harbaum/ftduino/addons/i2c-expander/ftduino+txt.jpg

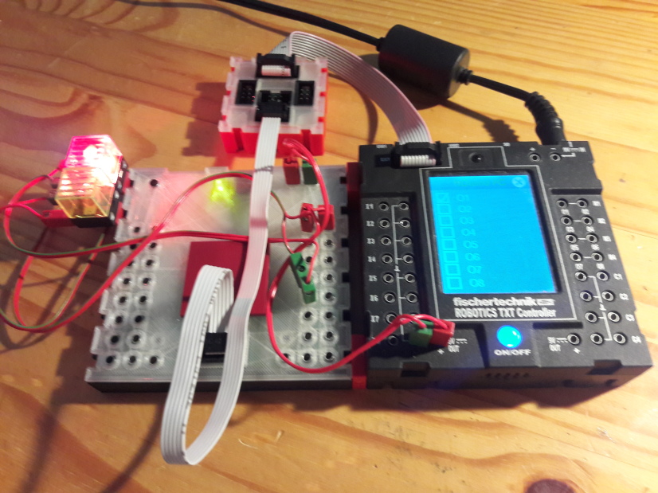
addons/i2c-expander/ftduino+txt.jpg
