harbaum/ftduino/doc/beispiele_ftduino.png

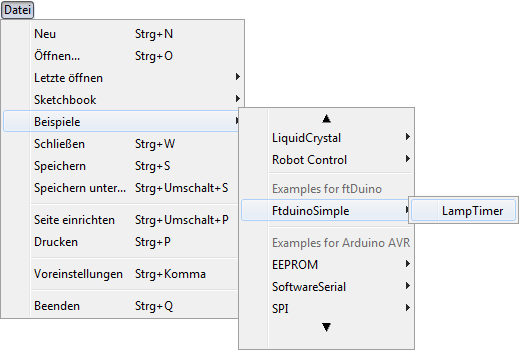
doc/beispiele_ftduino.png
