harbaum/ftduino/doc/ftduino_pcb_1.0.jpg

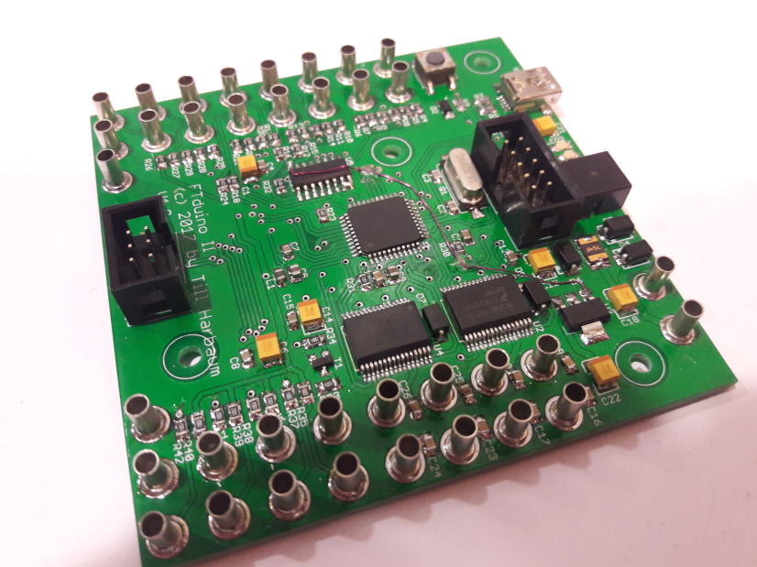
doc/ftduino_pcb_1.0.jpg
