harbaum/ftduino/webusb/images/webusb_board.png

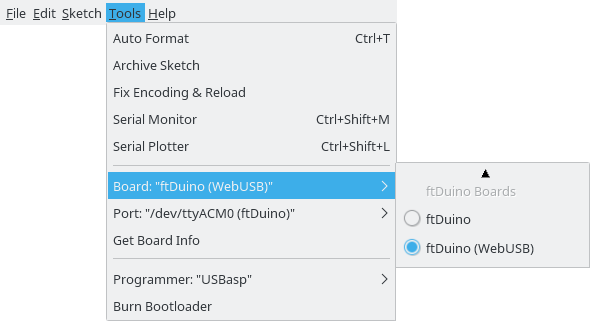
webusb/images/webusb_board.png
