harbaum/ftduino/webusb/images/webusb_examples.png

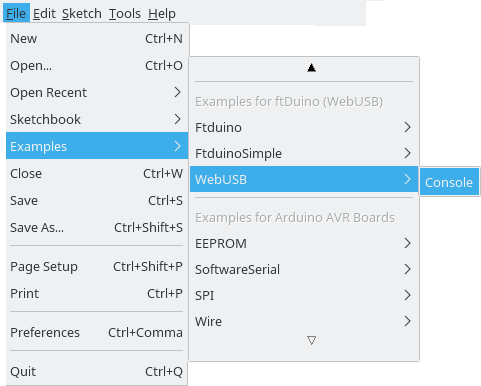
webusb/images/webusb_examples.png
