harbaum/ftduino/www/blue/images/ftduino_modul.jpg

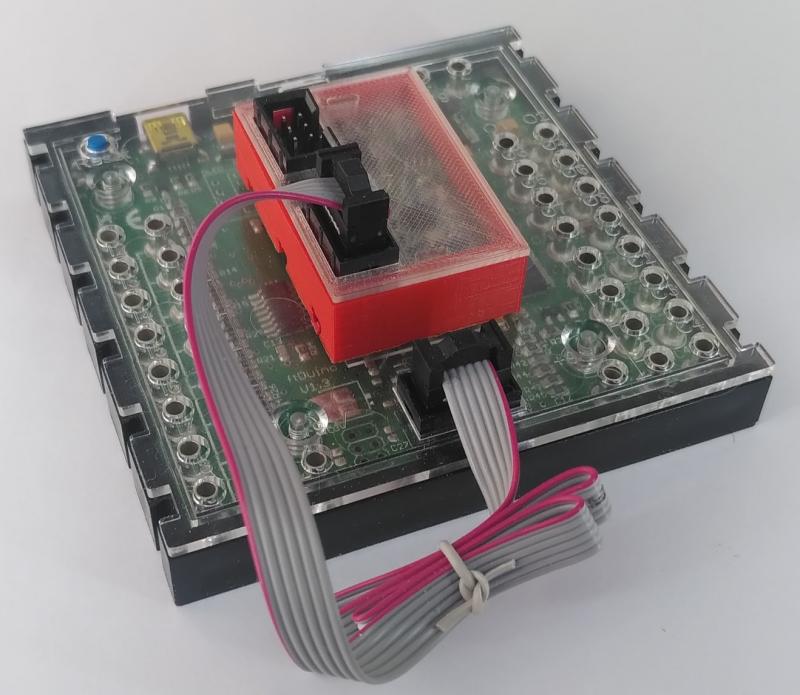
www/blue/images/ftduino_modul.jpg
