harbaum/ftduino/www/blue/images/ftduino_robot.jpg

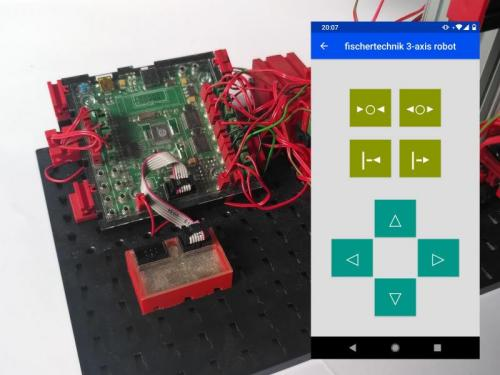
www/blue/images/ftduino_robot.jpg
