harbaum/ftduino/www/blue/images/ftduinoblue_buttons.png

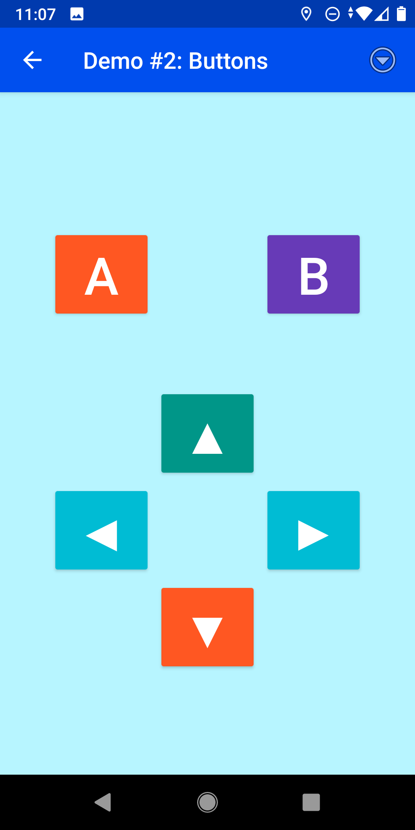
www/blue/images/ftduinoblue_buttons.png
