harbaum/ftduino/www/blue/images/ftduinoblue_demos.png

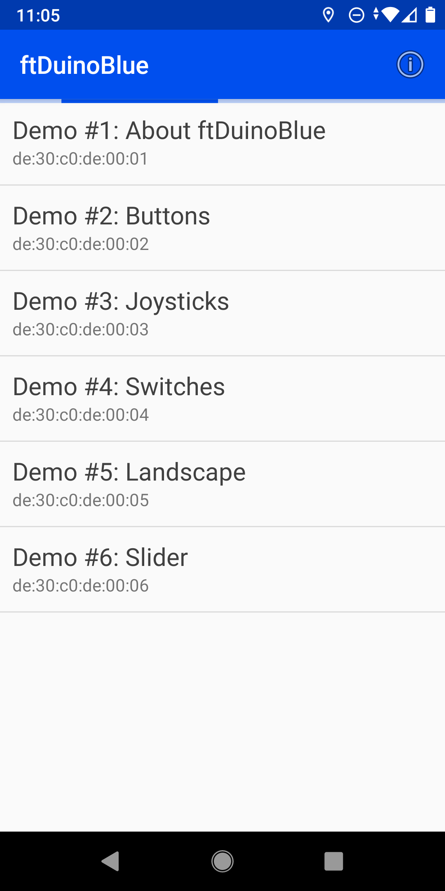
www/blue/images/ftduinoblue_demos.png
