harbaum/ftduino/www/blue/images/ftduinoblue_init.png

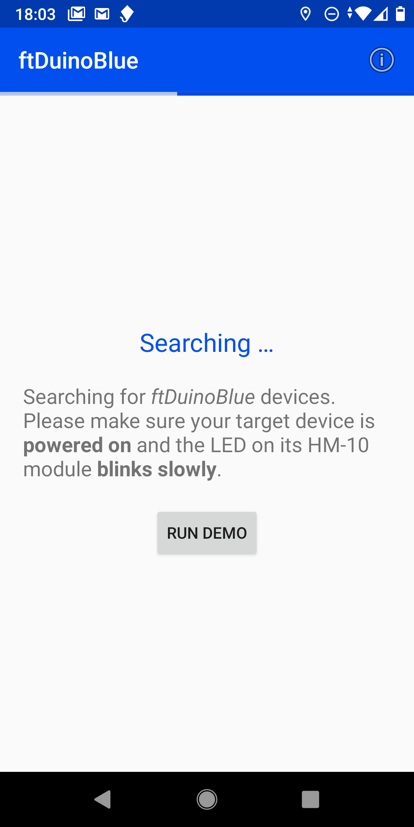
www/blue/images/ftduinoblue_init.png
