harbaum/ftduino/www/blue/images/ftduinoblue_introduction.png

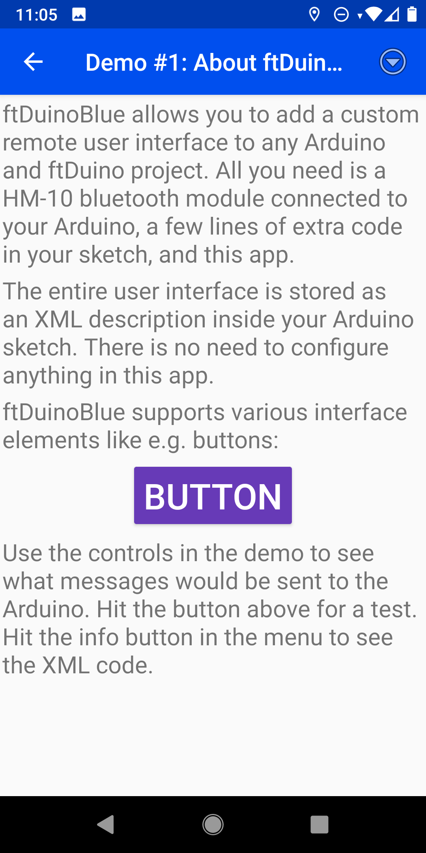
www/blue/images/ftduinoblue_introduction.png
