harbaum/ftduino/www/blue/images/ftduinoblue_joystick.png

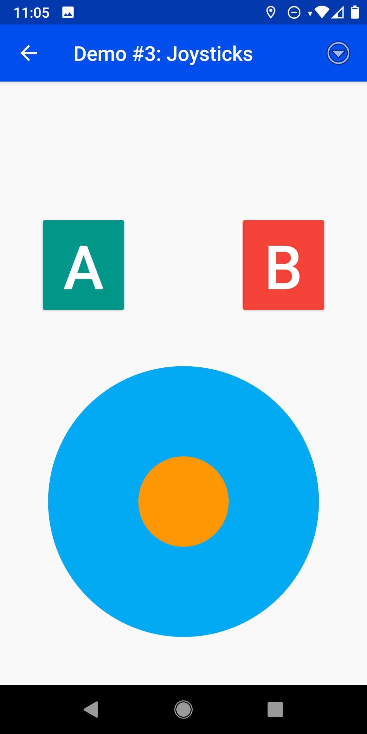
www/blue/images/ftduinoblue_joystick.png
