harbaum/ftduino/www/blue/images/ftduinoblue_landscape.png

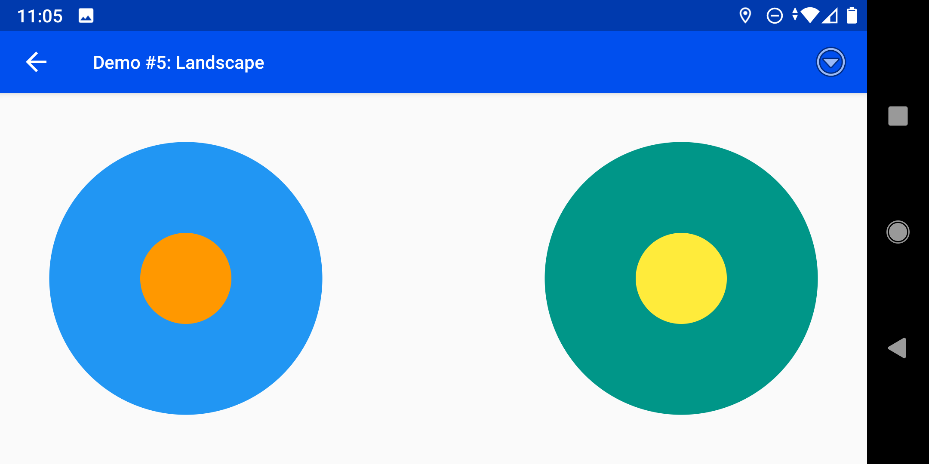
www/blue/images/ftduinoblue_landscape.png
