harbaum/ftduino/www/blue/images/ftduinoblue_sliders.png

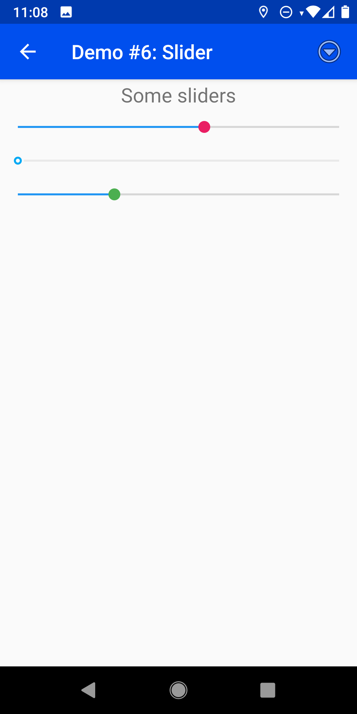
www/blue/images/ftduinoblue_sliders.png
