harbaum/ftduino/www/blue/images/ftduinoblue_switches.png

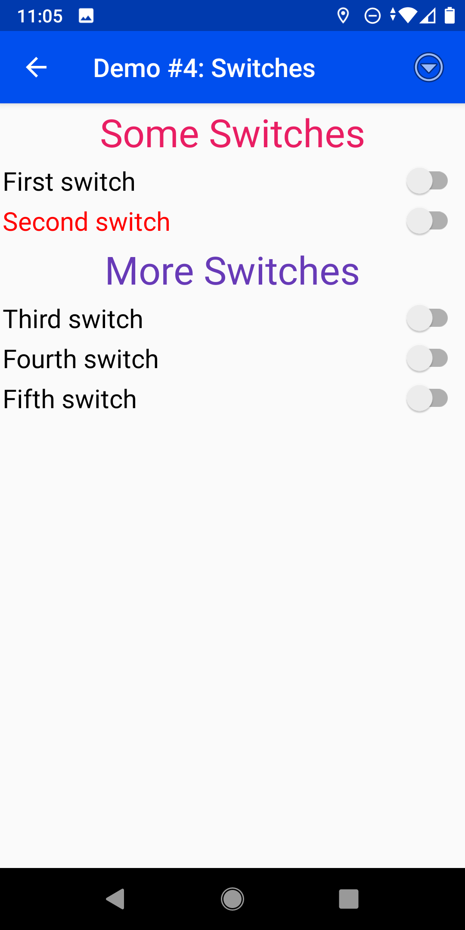
www/blue/images/ftduinoblue_switches.png
