harbaum/ftduino/www/blue/images/ftduinoblue_uno.jpg

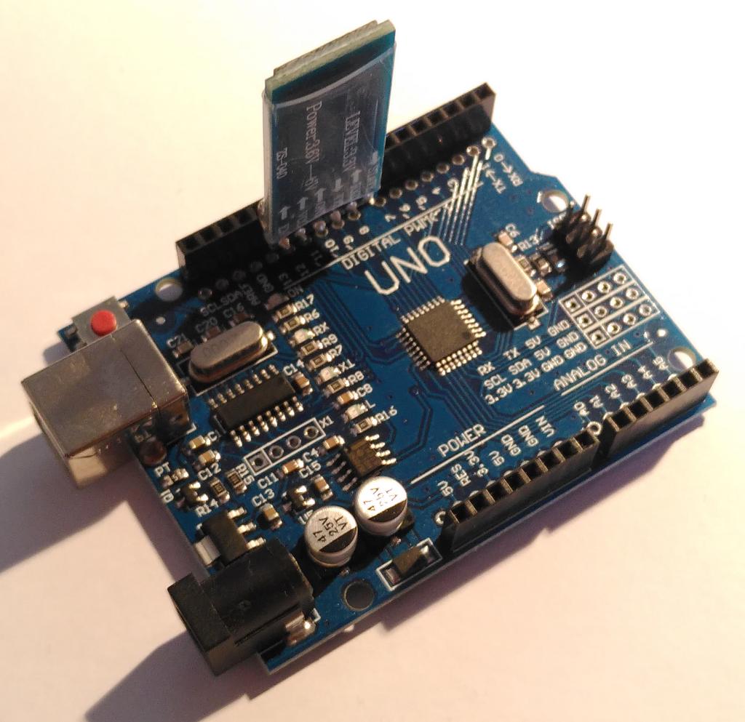
www/blue/images/ftduinoblue_uno.jpg
