harbaum/ftduino/www/blue/images/ftduinoblue_uno.png

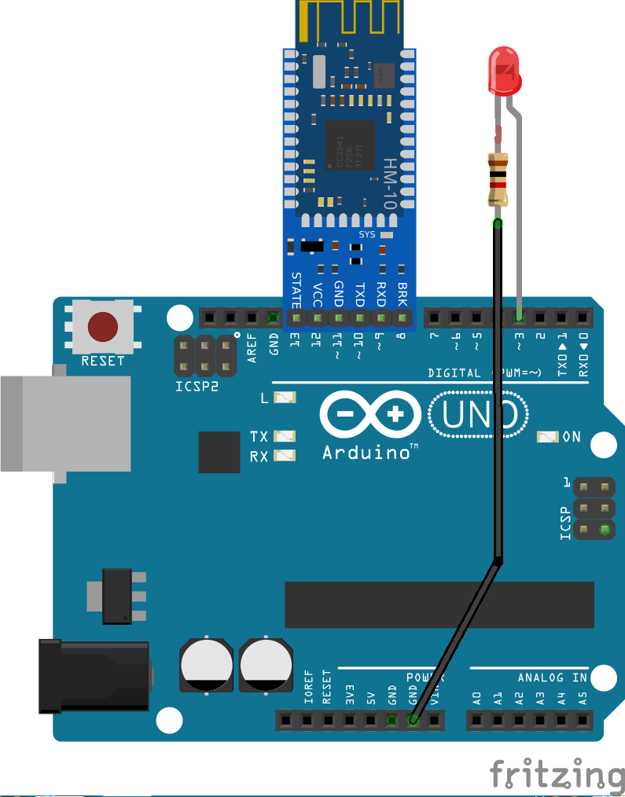
www/blue/images/ftduinoblue_uno.png
