harbaum/ftduino/www/blue/images/screenshot_demo.png

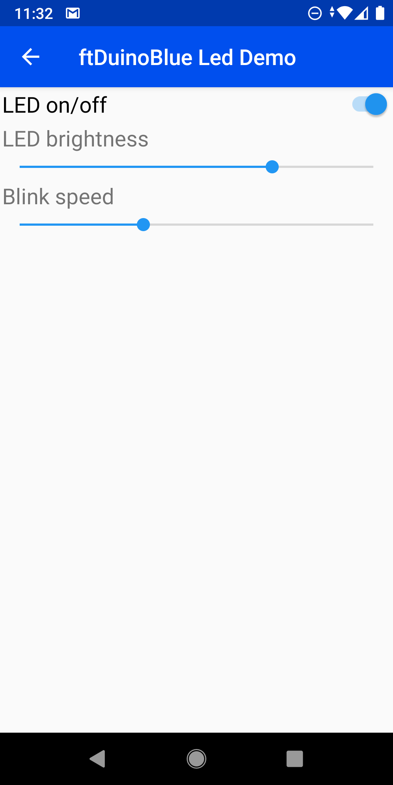
www/blue/images/screenshot_demo.png
