harbaum/ftduino/www/images/anschluesse.png

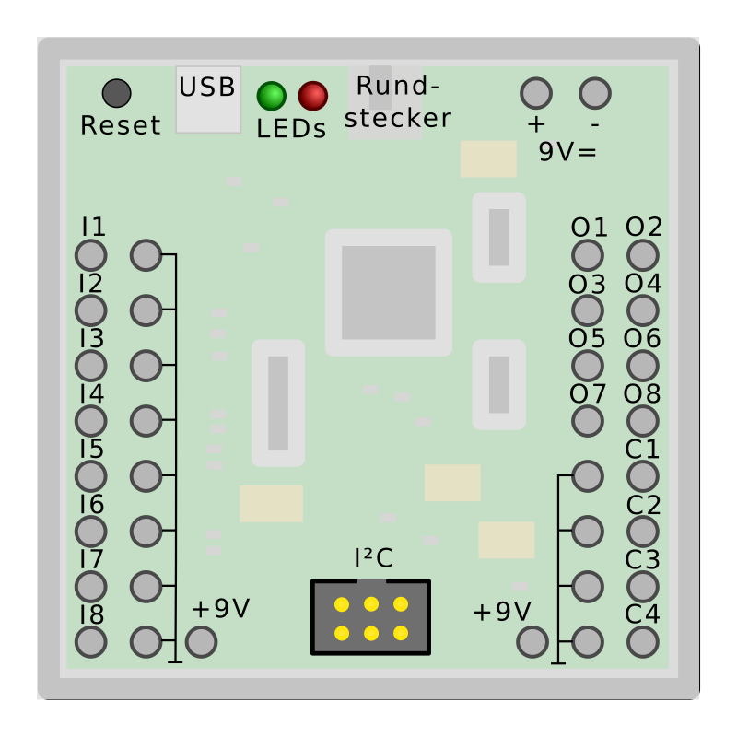
www/images/anschluesse.png
