harbaum/ftduino/www/images/ftduino.jpg

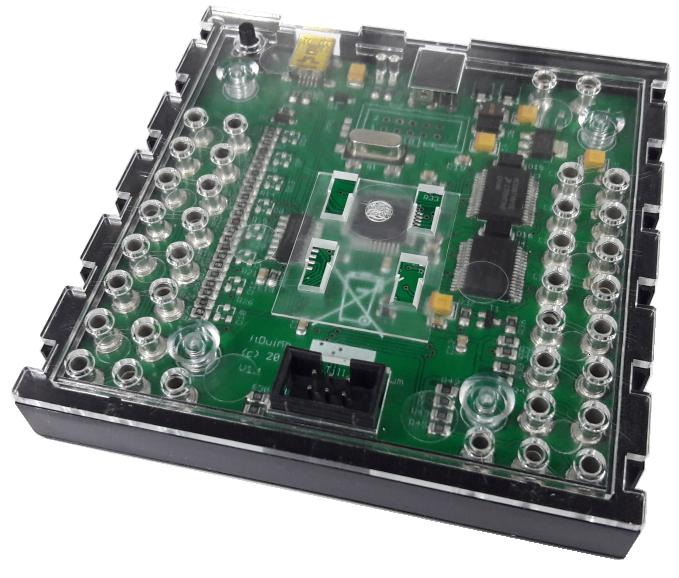
www/images/ftduino.jpg
