harbaum/ftduino/www/images/ide.png

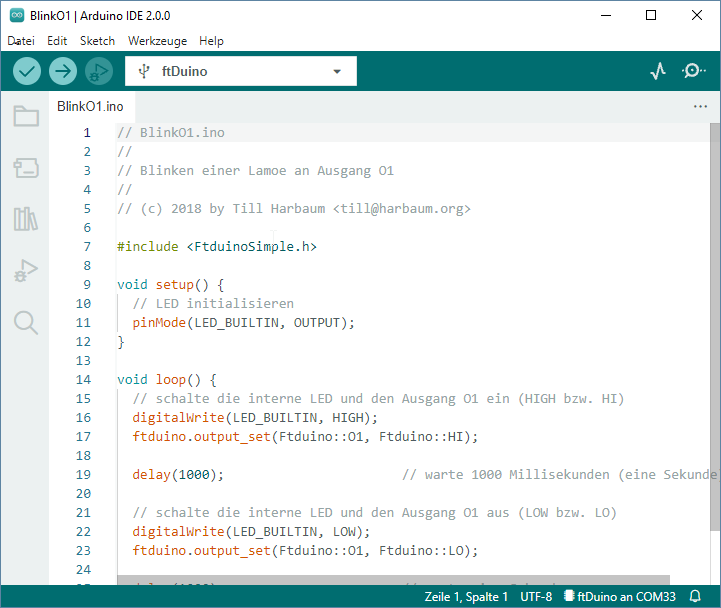
www/images/ide.png
