harbaum/ftduino/www/images/minecraft.jpg

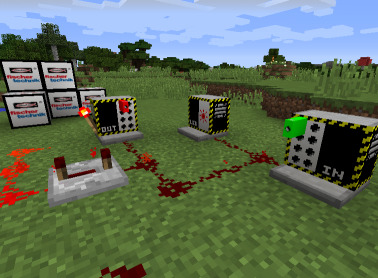
www/images/minecraft.jpg
