harbaum/ftduino/www/images/s4a_sprite.png

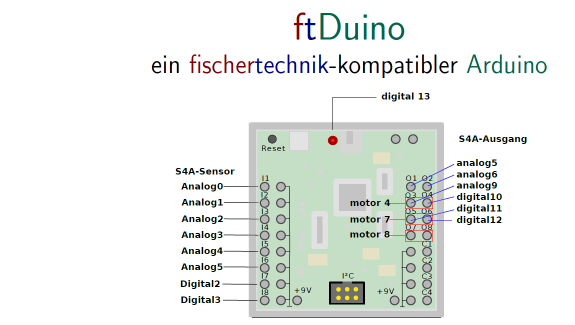
www/images/s4a_sprite.png
