harbaum/ftduino/www/images/scratch3_ftduino1.png

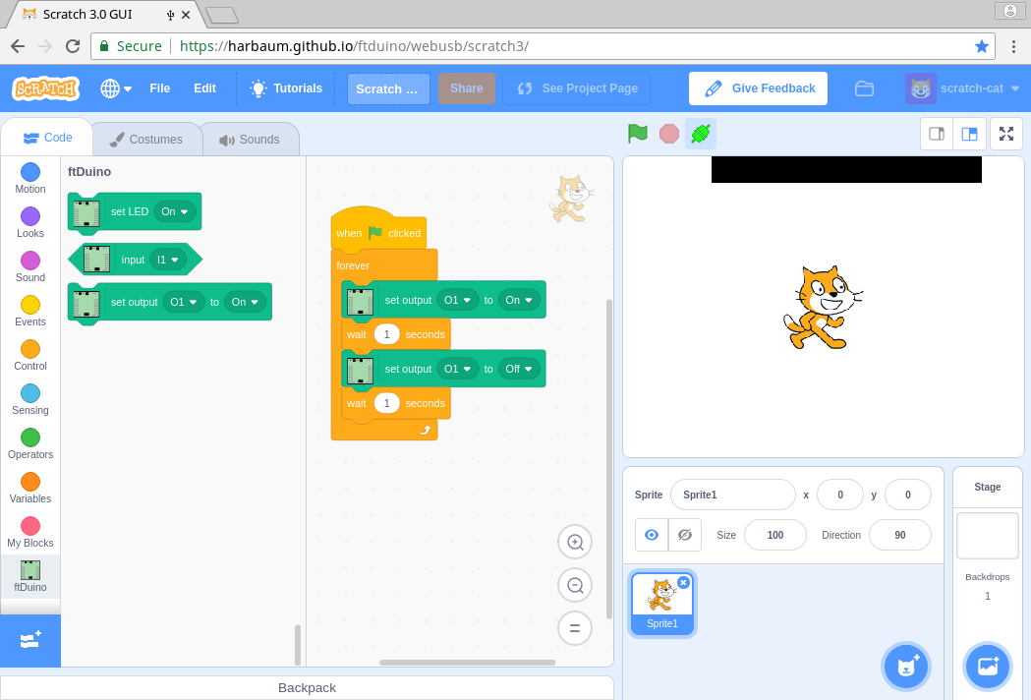
www/images/scratch3_ftduino1.png
