harbaum/ftduino/www/manual/anhang/ftduino_1_1_schematic_pdf.png

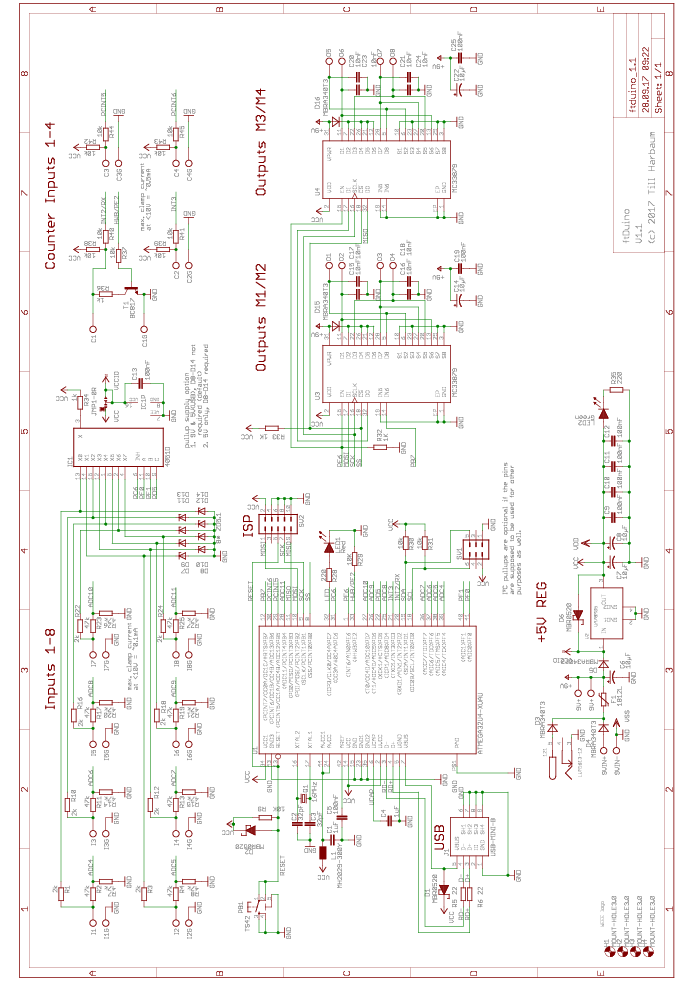
www/manual/anhang/ftduino_1_1_schematic_pdf.png
