harbaum/ftduino/www/manual/anhang/ftduino_1_1_parts_pdf.png

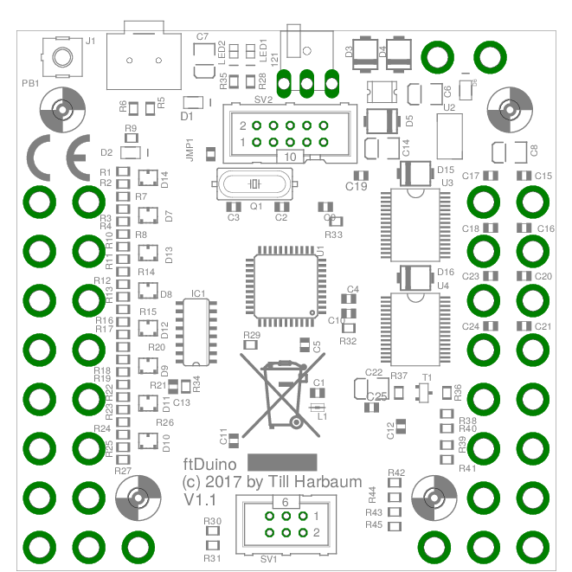
www/manual/anhang/ftduino_1_1_parts_pdf.png
