harbaum/ftduino/case/reset_button.stl

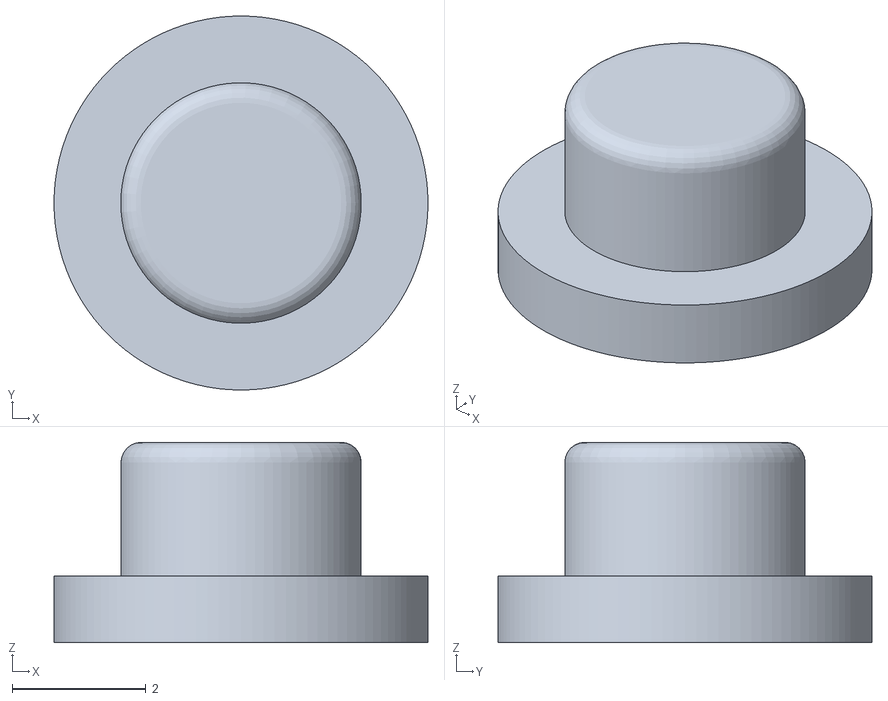
[picture p69: CAD file, 2017-12-19]
case/reset_button.stl
5.60 x 5.60 x 3.00
