harbaum/ftduino/case/bottom.stl

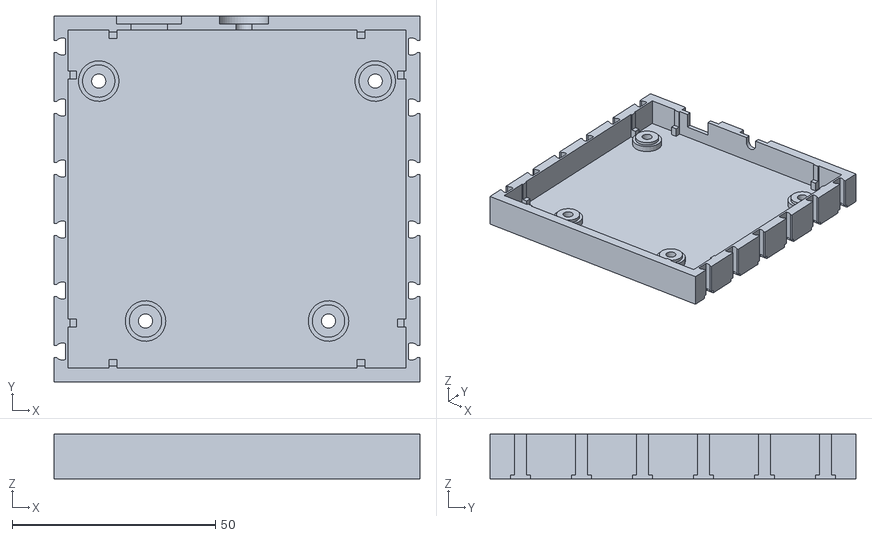
[picture p70: CAD file, 2017-12-19]
case/bottom.stl
90.0 x 90.0 x 11.0
