harbaum/ftduino/addons/vl53l0x/bottom.fcstd

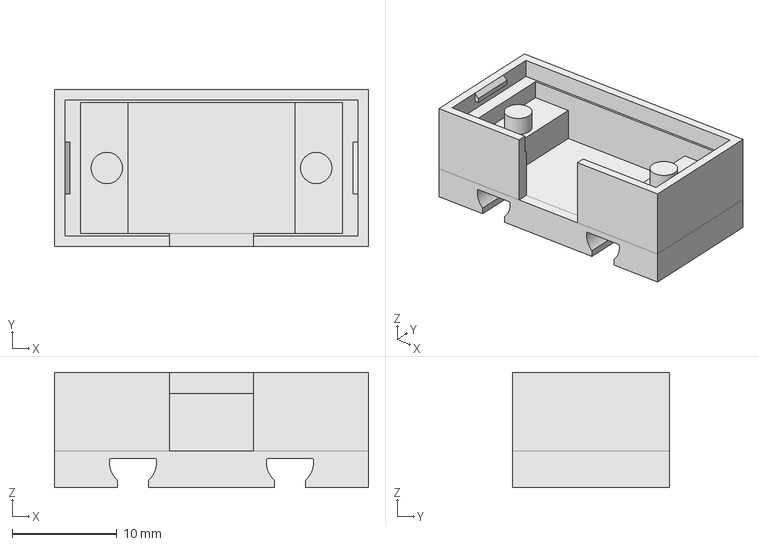
[picture p71: CAD file, 2018-03-22, an earlier design]
addons/vl53l0x/bottom.fcstd
30.0 x 15.0 x 11.0 mm
