harbaum/ftduino/www/manual/anhang/bottom_drawing_pdf.png

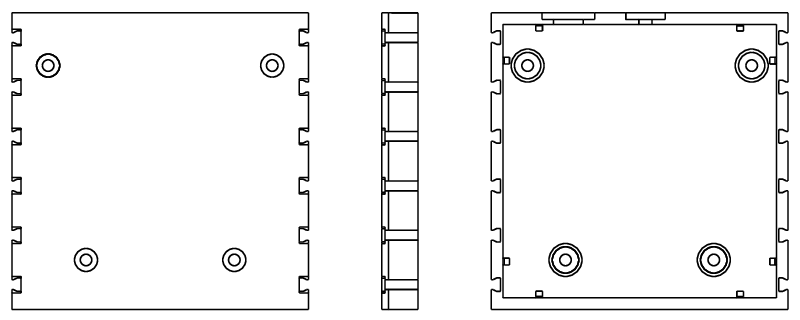
www/manual/anhang/bottom_drawing_pdf.png
