harbaum/ftduino/www/manual/anhang/ftduino_1_1_board_pdf.png

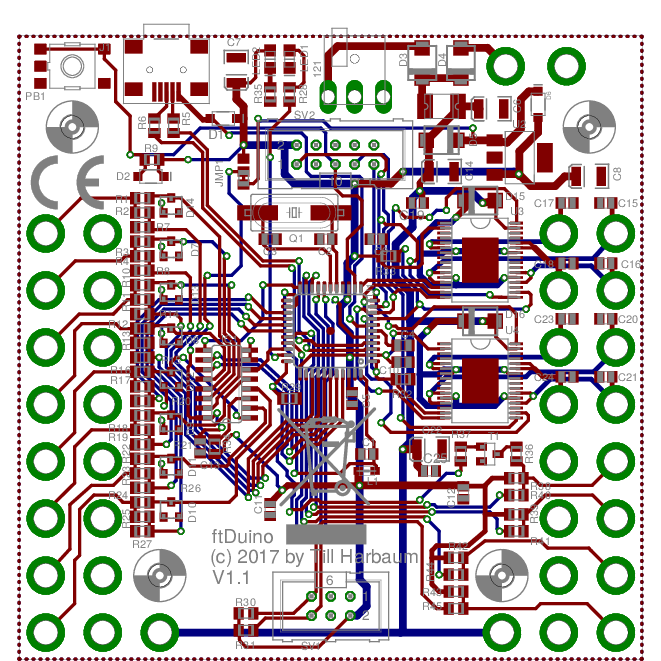
www/manual/anhang/ftduino_1_1_board_pdf.png
