harbaum/ftduino/www/manual/anhang/ftduino_1_1_dimensions_svg.png

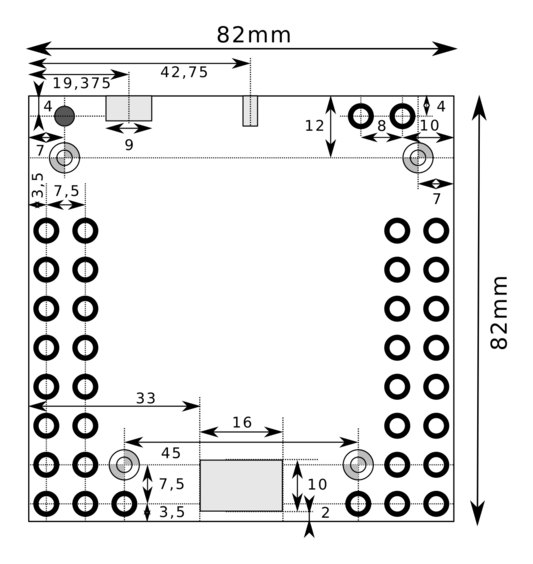
www/manual/anhang/ftduino_1_1_dimensions_svg.png
