harbaum/ftduino/www/manual/anhang/ftduino_1_1_masse_svg.png

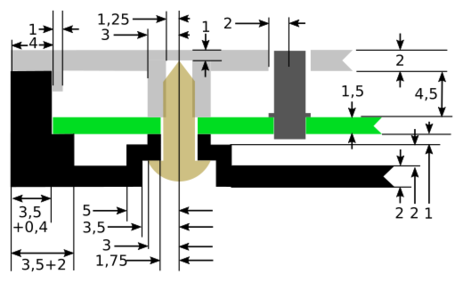
www/manual/anhang/ftduino_1_1_masse_svg.png
