harbaum/ftduino/www/manual/anhang/top_drawing_pdf.png

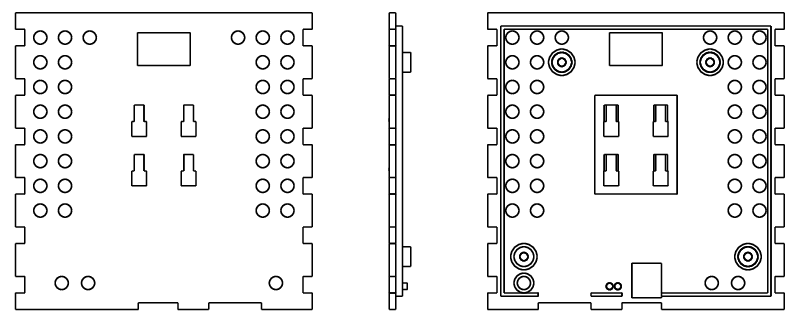
www/manual/anhang/top_drawing_pdf.png
