harbaum/ftduino/www/manual/aufbau/9v5v_svg.png

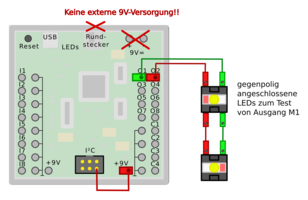
www/manual/aufbau/9v5v_svg.png
