harbaum/ftduino/www/manual/aufbau/inputs_svg.png

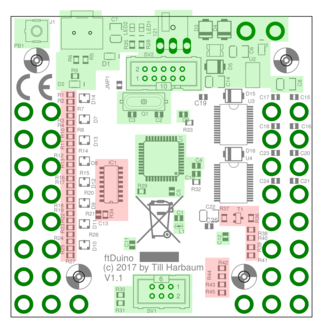
www/manual/aufbau/inputs_svg.png
