harbaum/ftduino/www/manual/aufbau/outputs_svg.png

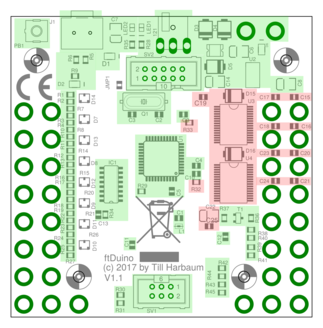
www/manual/aufbau/outputs_svg.png
