harbaum/ftduino/www/manual/aufbau/supply_svg.png

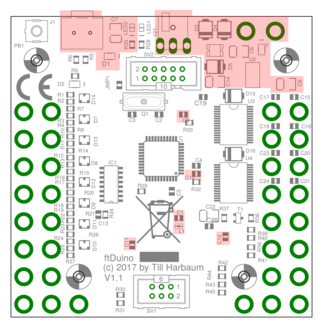
www/manual/aufbau/supply_svg.png
