harbaum/ftduino/www/manual/community/ftduinio.png

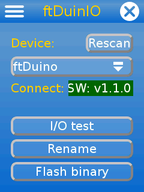
www/manual/community/ftduinio.png
