harbaum/ftduino/www/manual/community/ftExtender.jpeg

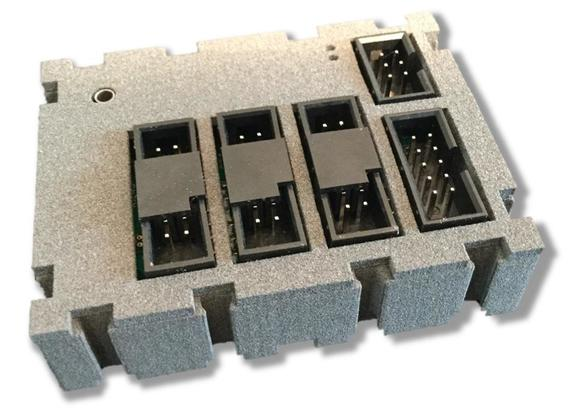
www/manual/community/ftExtender.jpeg
