harbaum/ftduino/www/manual/community/minecraft.png

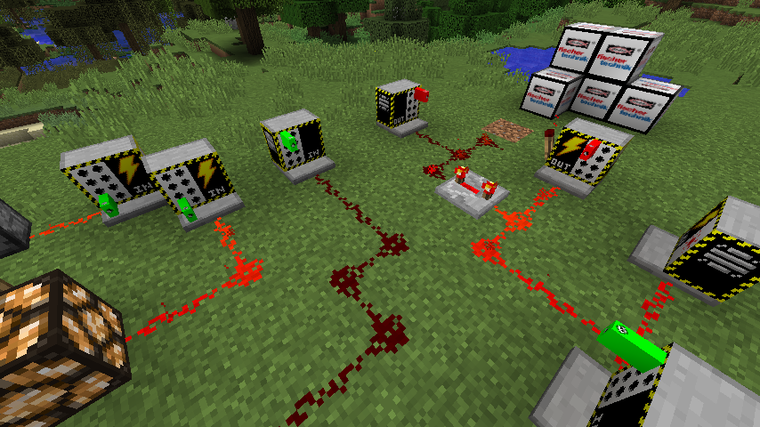
www/manual/community/minecraft.png
