harbaum/ftduino/www/manual/community/minecraft_input.png

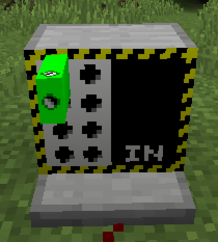
www/manual/community/minecraft_input.png
