harbaum/ftduino/www/manual/community/minecraft_led.png

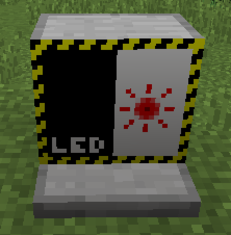
www/manual/community/minecraft_led.png
