harbaum/ftduino/www/manual/community/minecraft_output.png

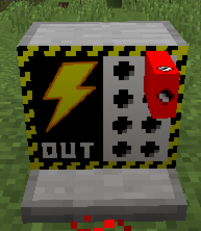
www/manual/community/minecraft_output.png
