harbaum/ftduino/www/manual/community/s4a.png

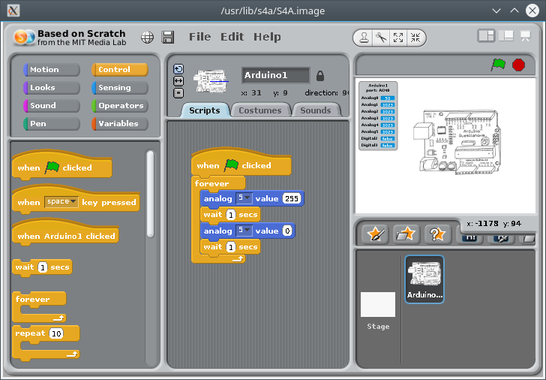
www/manual/community/s4a.png
