harbaum/ftduino/www/manual/community/s4a_beispiel_svg.png

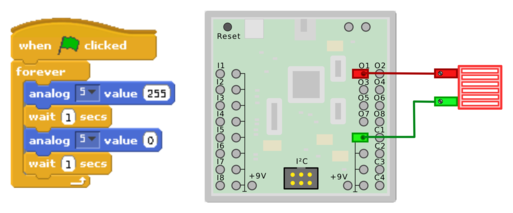
www/manual/community/s4a_beispiel_svg.png
