harbaum/ftduino/www/manual/community/s4a_gui.png

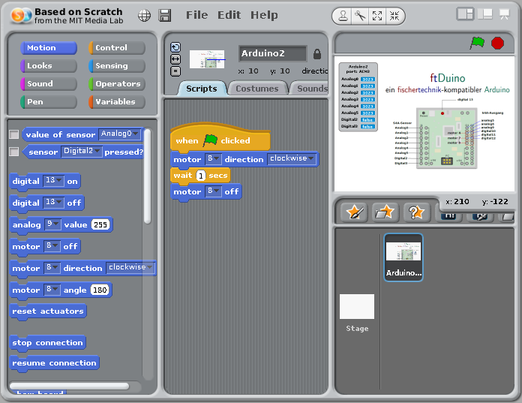
www/manual/community/s4a_gui.png
