harbaum/ftduino/www/manual/community/s4a_pins_svg.png

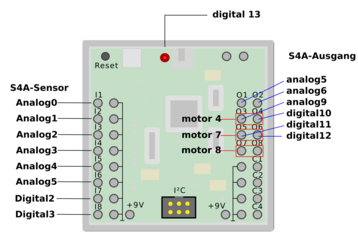
www/manual/community/s4a_pins_svg.png
