harbaum/ftduino/www/manual/community/s4a_sprite.png

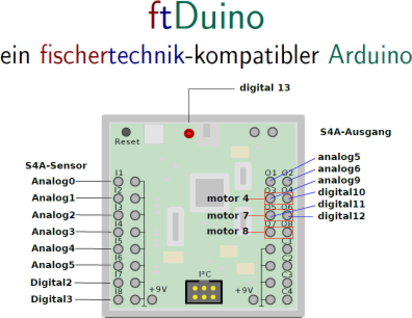
www/manual/community/s4a_sprite.png
