harbaum/ftduino/www/manual/community/startIDE01.png

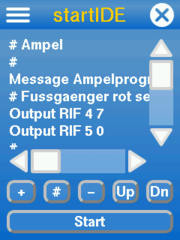
www/manual/community/startIDE01.png
