harbaum/ftduino/www/manual/community/startIDE02.png

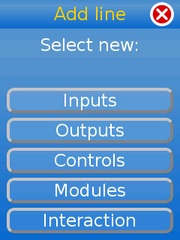
www/manual/community/startIDE02.png
