harbaum/ftduino/www/manual/community/startIDE03.png

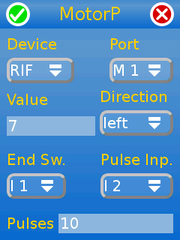
www/manual/community/startIDE03.png
