harbaum/ftduino/www/manual/controller/adafruit_gfx.png

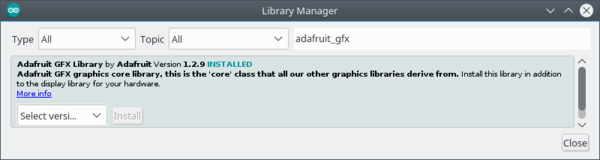
www/manual/controller/adafruit_gfx.png
