harbaum/ftduino/www/manual/controller/alte_trafos.jpg

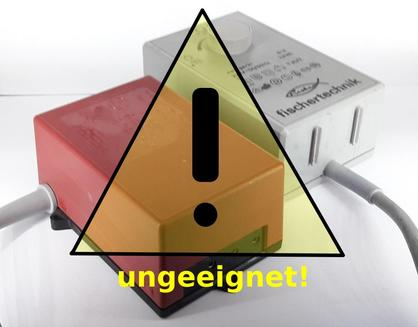
www/manual/controller/alte_trafos.jpg
