harbaum/ftduino/www/manual/controller/anschluesse_svg.png

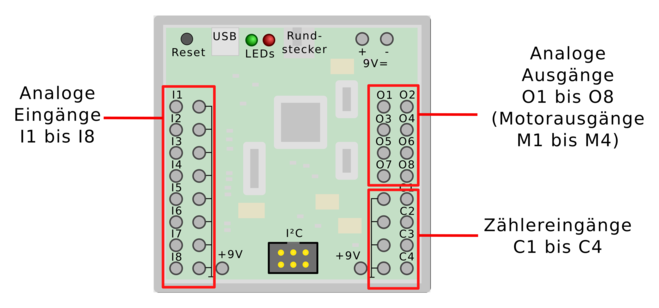
www/manual/controller/anschluesse_svg.png
