harbaum/ftduino/www/manual/controller/ausfuehrliche_ausgabe.png

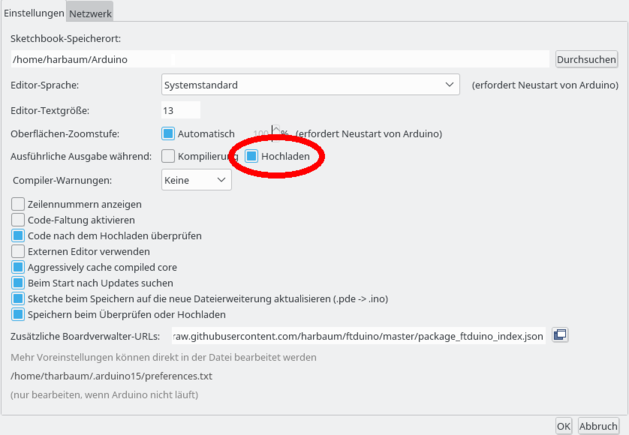
www/manual/controller/ausfuehrliche_ausgabe.png
