harbaum/ftduino/www/manual/controller/dritthersteller.jpg

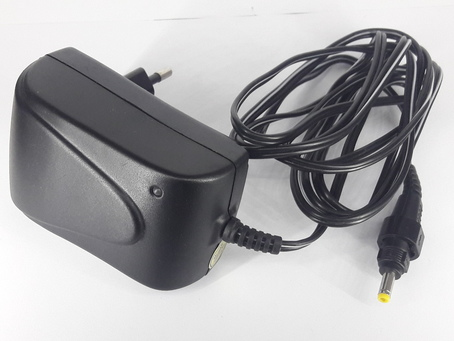
www/manual/controller/dritthersteller.jpg
