harbaum/ftduino/www/manual/controller/fehler_beim_hochladen.png

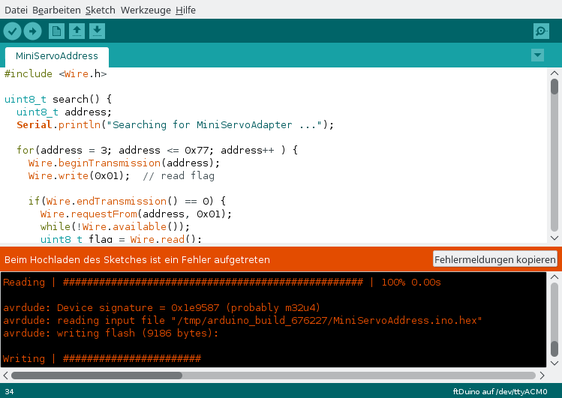
www/manual/controller/fehler_beim_hochladen.png
