harbaum/ftduino/www/manual/controller/ft_trafo_1.jpg

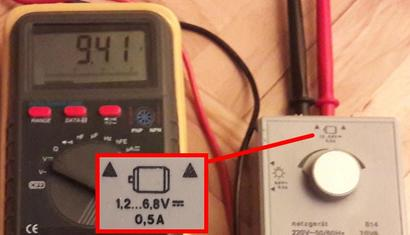
www/manual/controller/ft_trafo_1.jpg
