harbaum/ftduino/www/manual/controller/ft_trafo_2.jpg

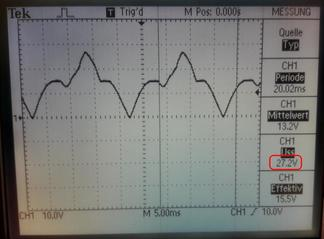
www/manual/controller/ft_trafo_2.jpg
