harbaum/ftduino/www/manual/controller/ft_versorgungen.jpg

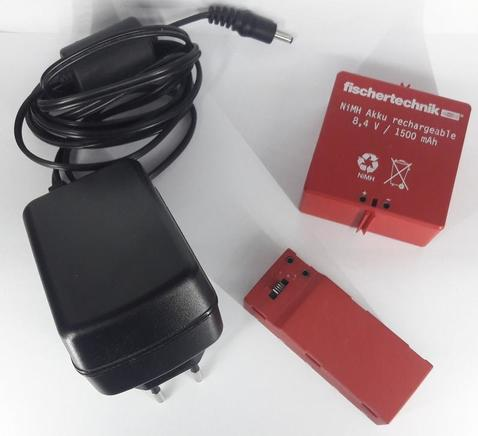
www/manual/controller/ft_versorgungen.jpg
