harbaum/ftduino/www/manual/controller/i2c-kappe.jpg

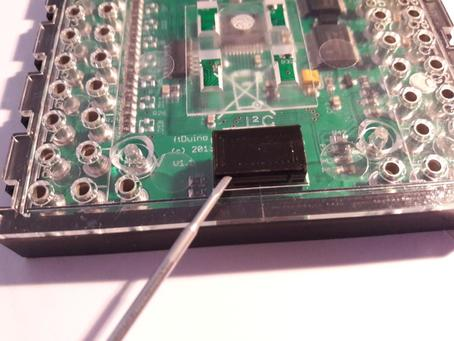
www/manual/controller/i2c-kappe.jpg
