harbaum/ftduino/www/manual/controller/leonardo.jpg

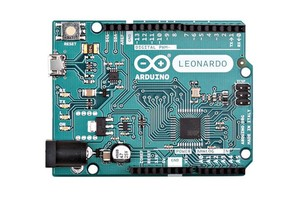
www/manual/controller/leonardo.jpg
