harbaum/ftduino/www/manual/controller/oled.jpg

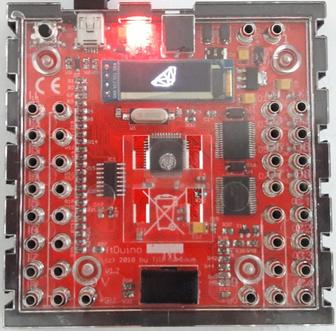
www/manual/controller/oled.jpg
