harbaum/ftduino/www/manual/controller/schema_svg.png

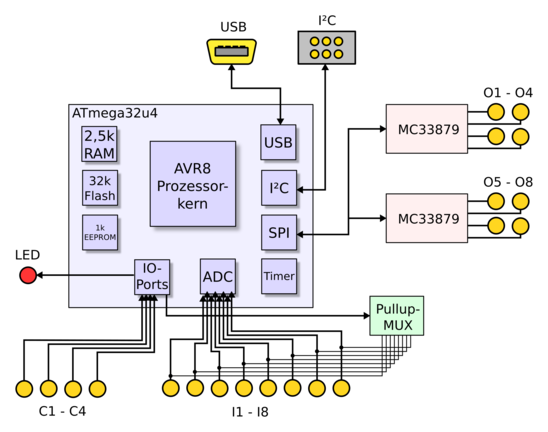
www/manual/controller/schema_svg.png
