harbaum/ftduino/www/manual/controller/stecker_svg.png

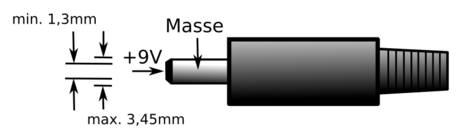
www/manual/controller/stecker_svg.png
