harbaum/ftduino/www/manual/controller/ultraschall_svg.png

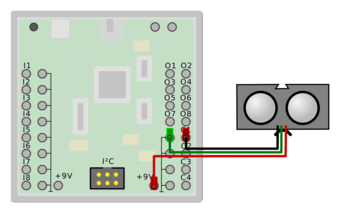
www/manual/controller/ultraschall_svg.png
