harbaum/ftduino/www/manual/controller/usb-anschluss.jpg

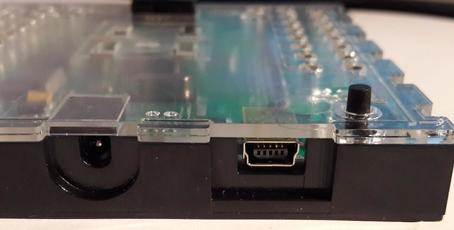
www/manual/controller/usb-anschluss.jpg
