harbaum/ftduino/www/manual/ersteschritte/input_i_svg.png

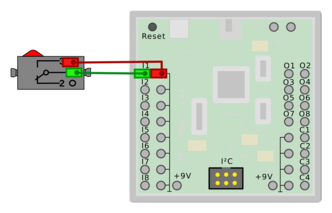
www/manual/ersteschritte/input_i_svg.png
