harbaum/ftduino/www/manual/ersteschritte/win10_portauswahl.png

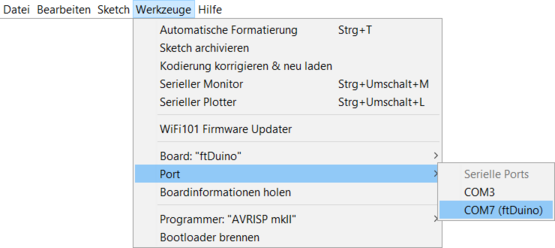
www/manual/ersteschritte/win10_portauswahl.png
