harbaum/ftduino/www/manual/ersteschritte/win10port.png

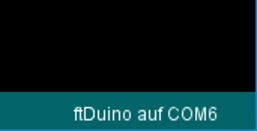
www/manual/ersteschritte/win10port.png
