harbaum/ftduino/www/manual/ersteschritte/zeilenenden.png

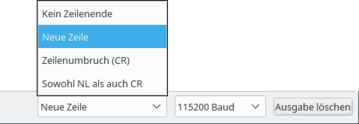
www/manual/ersteschritte/zeilenenden.png
