harbaum/ftduino/www/manual/experimente/installieren_midiusb.png

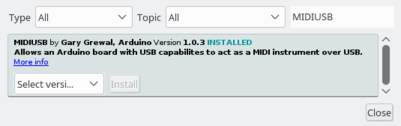
www/manual/experimente/installieren_midiusb.png
