harbaum/ftduino/www/manual/installation/auswahl_ftduino.png

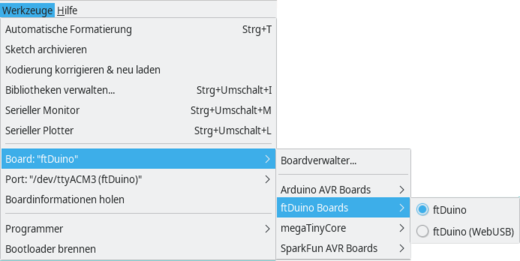
www/manual/installation/auswahl_ftduino.png
