harbaum/ftduino/www/manual/installation/driver_install.png

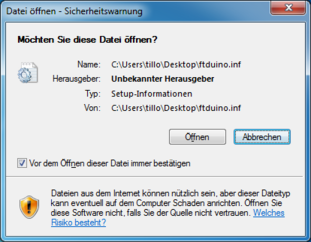
www/manual/installation/driver_install.png
