harbaum/ftduino/www/manual/installation/ide_voreinstellungen.png

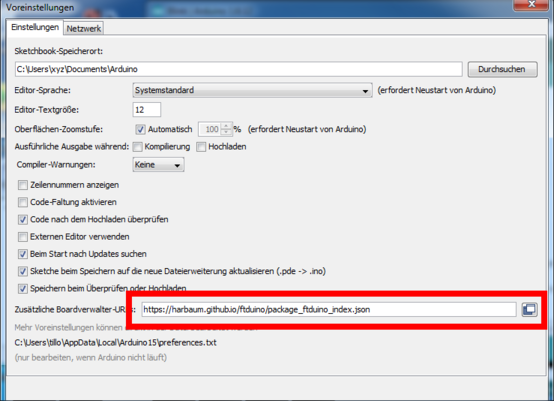
www/manual/installation/ide_voreinstellungen.png
