harbaum/ftduino/www/manual/installation/mac_ports.jpg

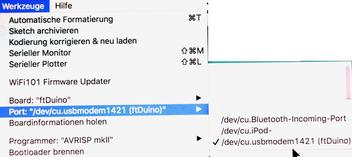
www/manual/installation/mac_ports.jpg
