harbaum/ftduino/www/manual/installation/sicherheitsabfrage.png

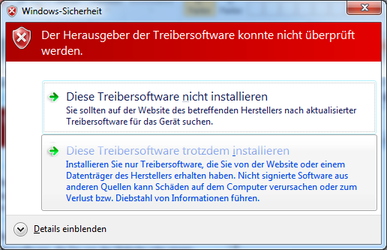
www/manual/installation/sicherheitsabfrage.png
