harbaum/ftduino/www/manual/installation/ubuntu_software_arduino.png

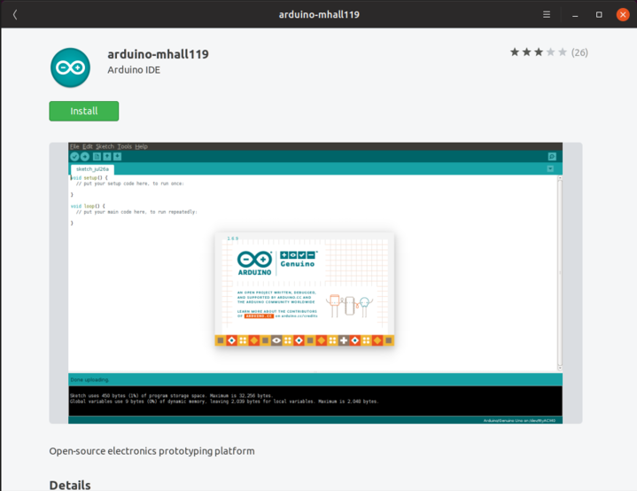
www/manual/installation/ubuntu_software_arduino.png
