harbaum/ftduino/www/manual/modelle/ampelzustand_svg.png

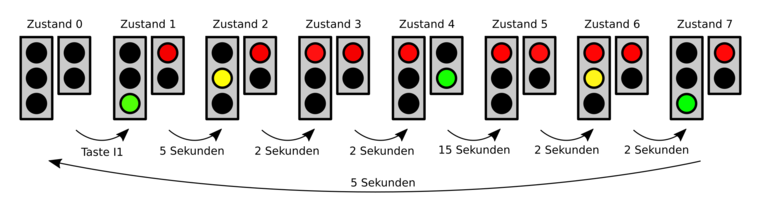
www/manual/modelle/ampelzustand_svg.png
