harbaum/ftduino/www/manual/modelle/idas_ampel.jpg

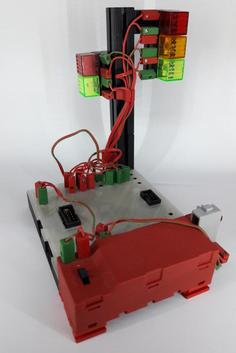
www/manual/modelle/idas_ampel.jpg
