harbaum/ftduino/www/manual/modelle/idas_ampel_svg.png

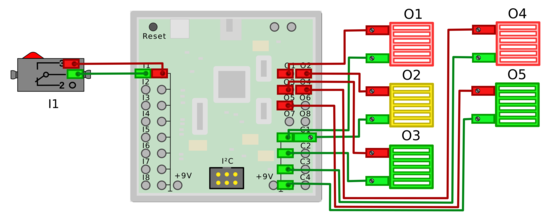
www/manual/modelle/idas_ampel_svg.png
