harbaum/ftduino/www/manual/modelle/plotter_detail.jpg

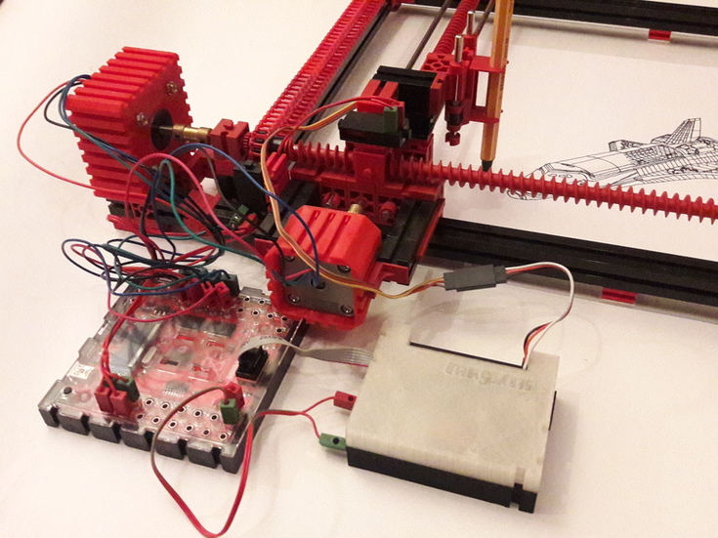
www/manual/modelle/plotter_detail.jpg
