harbaum/ftduino/www/manual/modelle/plotter_ganz.jpg

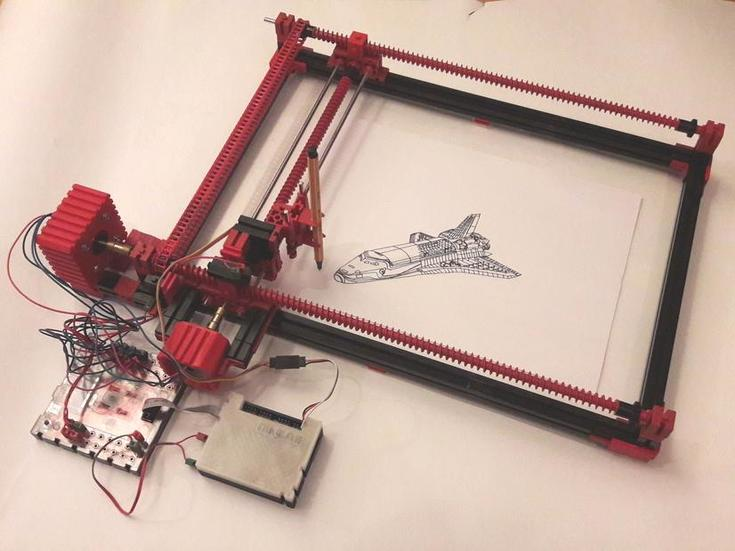
www/manual/modelle/plotter_ganz.jpg
