harbaum/ftduino/www/manual/programmierung/ampel_svg.png

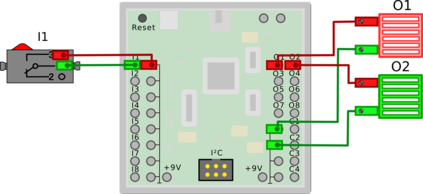
www/manual/programmierung/ampel_svg.png
