harbaum/ftduino/www/manual/programmierung/blinko1_auf_github.png

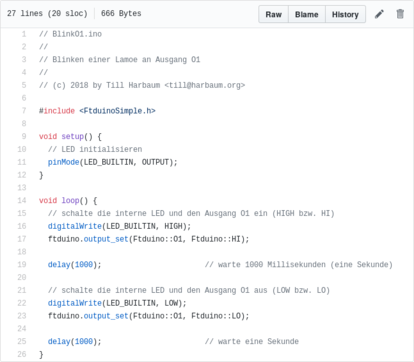
www/manual/programmierung/blinko1_auf_github.png
