harbaum/ftduino/www/manual/programmierung/blinko1_in_arduino_ide.png

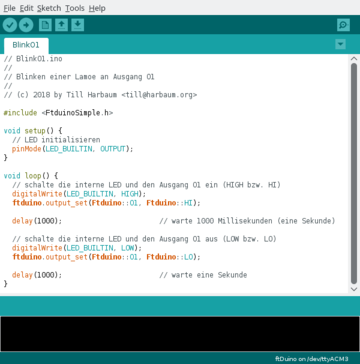
www/manual/programmierung/blinko1_in_arduino_ide.png
