harbaum/ftduino/www/manual/programmierung/button_compile.png

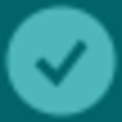
www/manual/programmierung/button_compile.png
