harbaum/ftduino/www/manual/programmierung/button_download.png

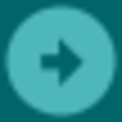
www/manual/programmierung/button_download.png
