harbaum/ftduino/www/manual/programmierung/cpp_blinko1.png

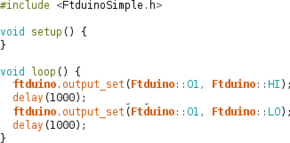
www/manual/programmierung/cpp_blinko1.png
