harbaum/ftduino/www/manual/programmierung/fehlermeldung.png

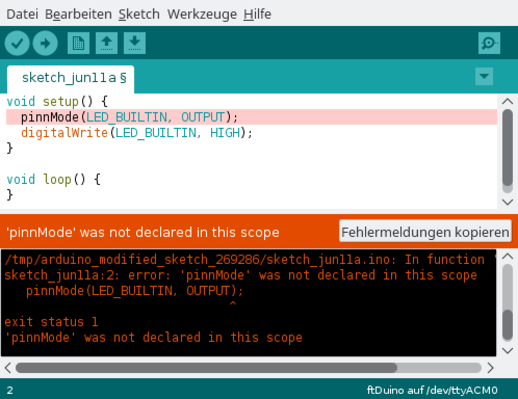
www/manual/programmierung/fehlermeldung.png
