harbaum/ftduino/www/manual/programmierung/funktionen_svg.png

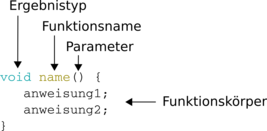
www/manual/programmierung/funktionen_svg.png
