harbaum/ftduino/www/manual/programmierung/output_o1_svg.png

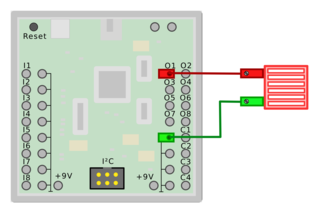
www/manual/programmierung/output_o1_svg.png
