harbaum/ftduino/www/manual/programmierung/robopro_blinko1.png

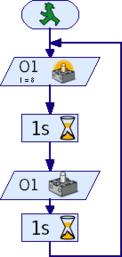
www/manual/programmierung/robopro_blinko1.png
