harbaum/ftduino/www/manual/programmierung/schranke_svg.png

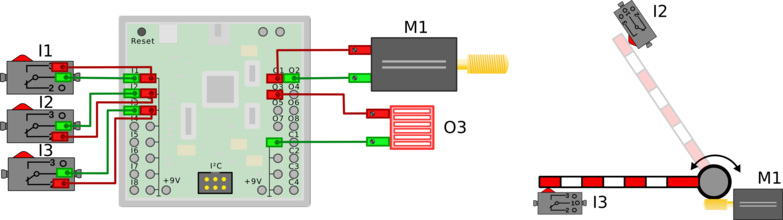
www/manual/programmierung/schranke_svg.png
