harbaum/ftduino/www/manual/programmierung/sketch-ablauf_svg.png

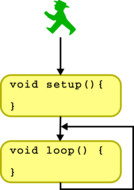
www/manual/programmierung/sketch-ablauf_svg.png
