harbaum/ftduino/www/manual/schule/arduino-ide.png

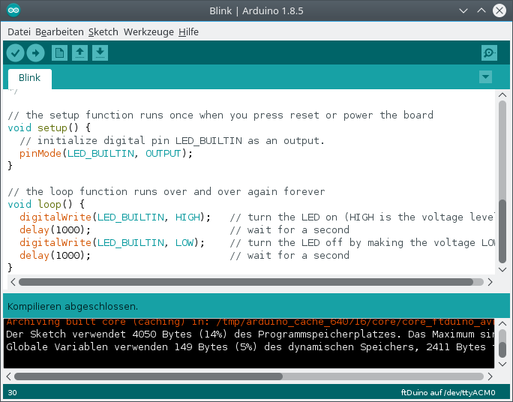
www/manual/schule/arduino-ide.png
