harbaum/ftduino/www/manual/schule/blockly.png

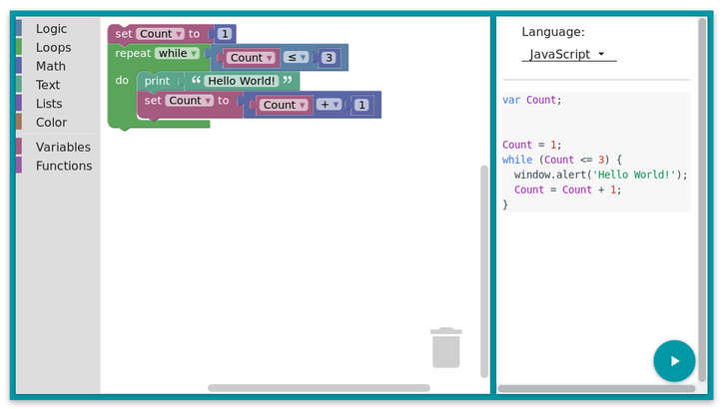
www/manual/schule/blockly.png
