harbaum/ftduino/www/manual/schule/brickly_lite.png

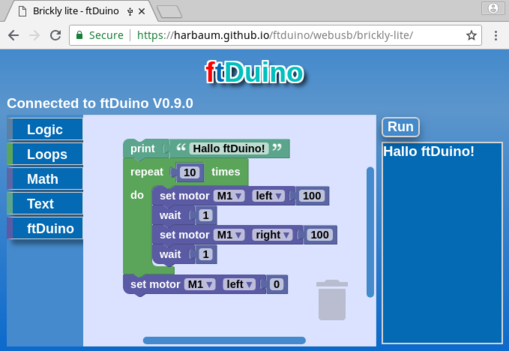
www/manual/schule/brickly_lite.png
