harbaum/ftduino/www/manual/schule/minecraft.png

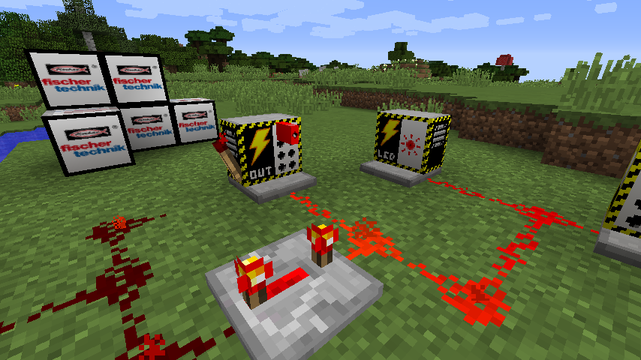
www/manual/schule/minecraft.png
