harbaum/ftduino/www/manual/schule/s30srv.png

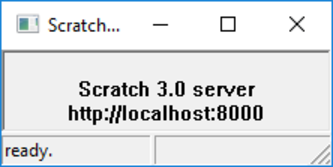
www/manual/schule/s30srv.png
