harbaum/ftduino/www/manual/schule/schwierigkeit_svg.png

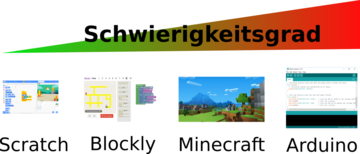
www/manual/schule/schwierigkeit_svg.png
