harbaum/ftduino/www/manual/schule/scratch3_extensions.png

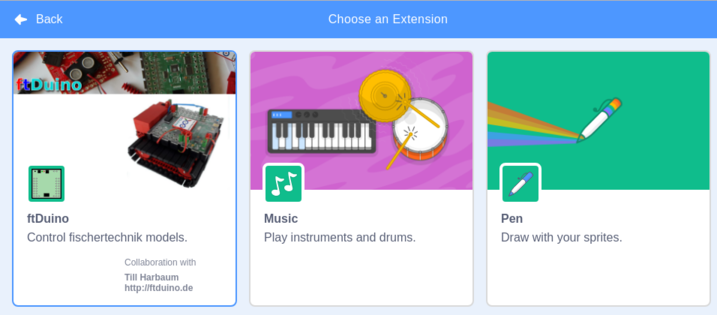
www/manual/schule/scratch3_extensions.png
