harbaum/ftduino/www/manual/schule/scratch3_main.png

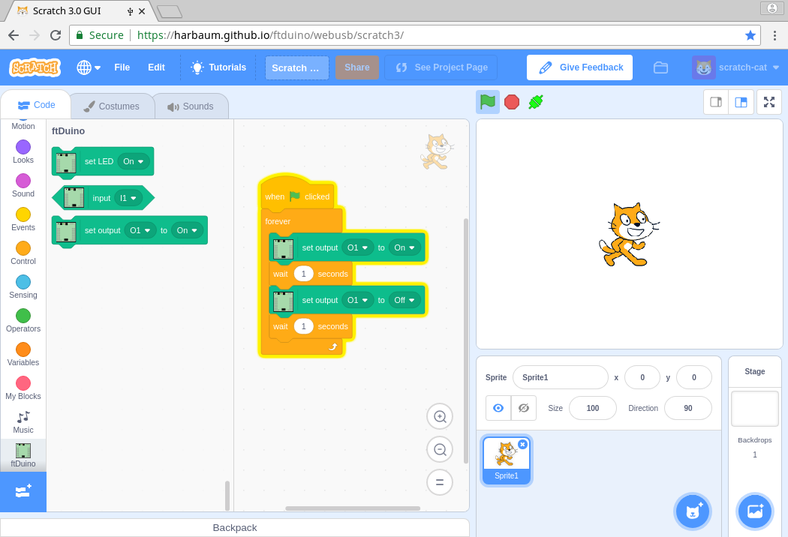
www/manual/schule/scratch3_main.png
