harbaum/ftduino/www/manual/schule/scratch_screenshot.png

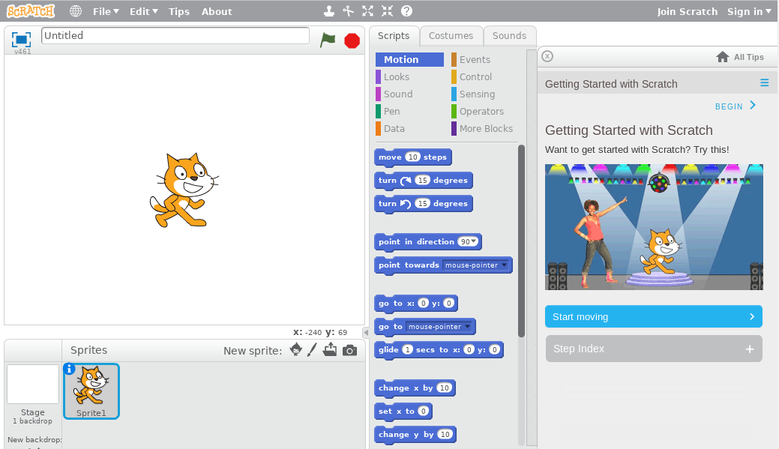
www/manual/schule/scratch_screenshot.png
