harbaum/ftduino/www/manual/experimente/android-screenshot.png

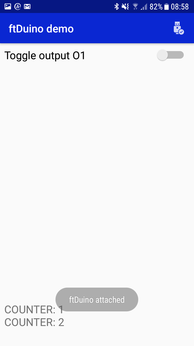
www/manual/experimente/android-screenshot.png
