harbaum/ftduino/www/manual/experimente/android.jpg

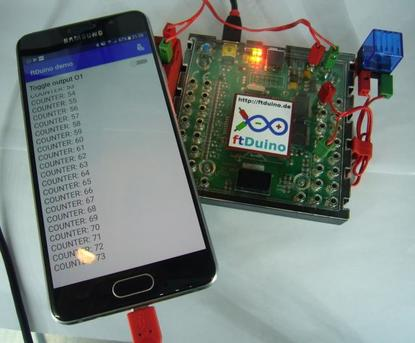
www/manual/experimente/android.jpg
