harbaum/ftduino/www/manual/experimente/bme680_foto.jpg

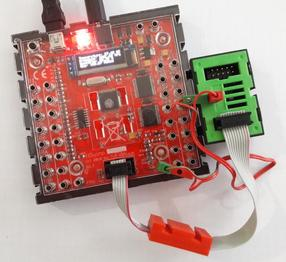
www/manual/experimente/bme680_foto.jpg
