harbaum/ftduino/www/manual/experimente/bme680_libs.png

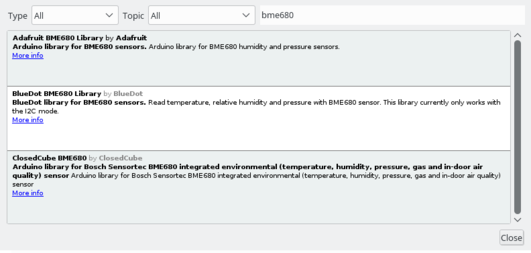
www/manual/experimente/bme680_libs.png
