harbaum/ftduino/www/manual/experimente/bme680_serial.png

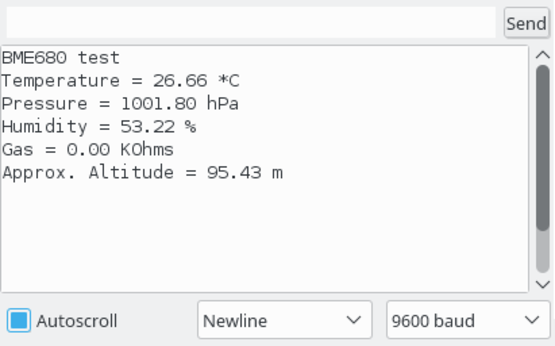
www/manual/experimente/bme680_serial.png
