harbaum/ftduino/www/manual/experimente/brickly_lite_tablet.jpg

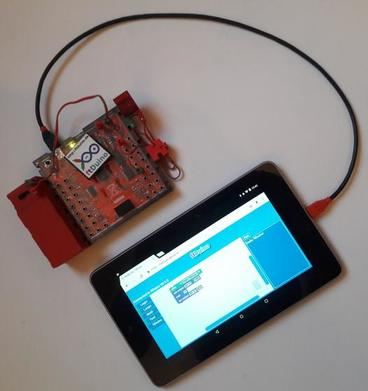
www/manual/experimente/brickly_lite_tablet.jpg
