harbaum/ftduino/www/manual/experimente/bt_module.jpg

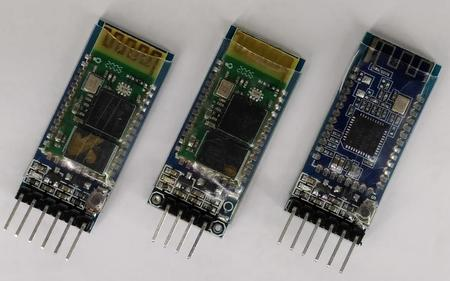
www/manual/experimente/bt_module.jpg
