harbaum/ftduino/www/manual/experimente/eingangsschaltung_pdf.png

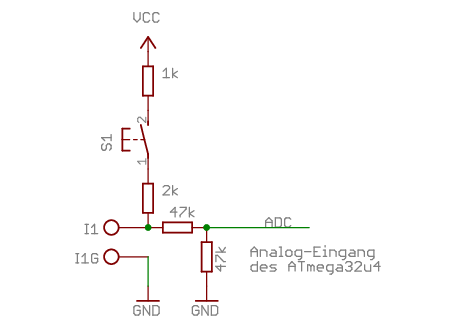
www/manual/experimente/eingangsschaltung_pdf.png
