harbaum/ftduino/www/manual/experimente/emergencystop_svg.png

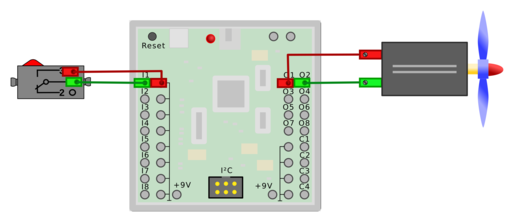
www/manual/experimente/emergencystop_svg.png
