harbaum/ftduino/www/manual/experimente/foto_mpu6050.jpg

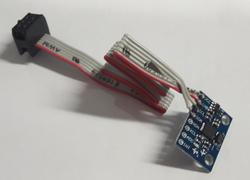
www/manual/experimente/foto_mpu6050.jpg
