harbaum/ftduino/www/manual/experimente/ftduino_hm10_c1.jpg

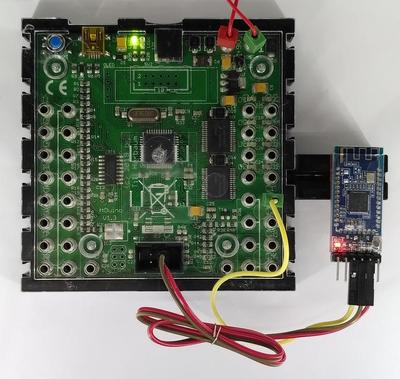
www/manual/experimente/ftduino_hm10_c1.jpg
