harbaum/ftduino/www/manual/experimente/ftduino_hm10_c1_c2.jpg

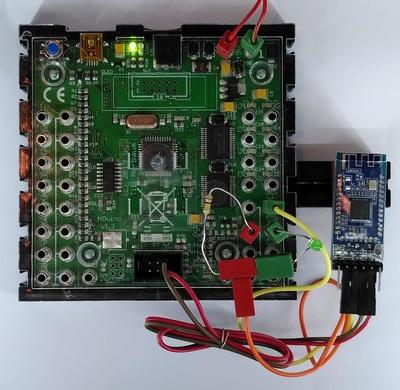
www/manual/experimente/ftduino_hm10_c1_c2.jpg
