harbaum/ftduino/www/manual/experimente/gamepad_svg.png

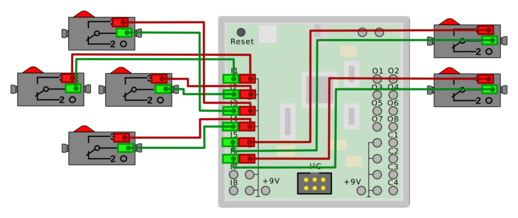
www/manual/experimente/gamepad_svg.png
