harbaum/ftduino/www/manual/experimente/hm10_atcmd.png

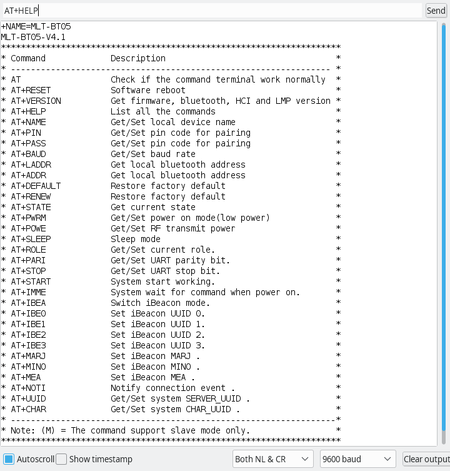
www/manual/experimente/hm10_atcmd.png
