harbaum/ftduino/www/manual/experimente/hm10_bidir_7805.jpg

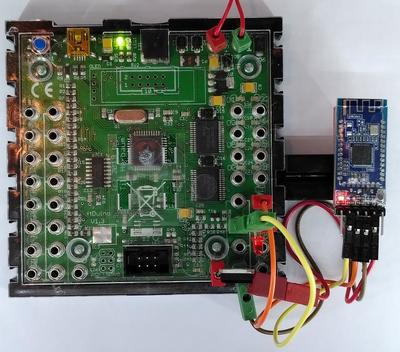
www/manual/experimente/hm10_bidir_7805.jpg
