harbaum/ftduino/www/manual/experimente/hm10_bidir_7805_2.jpg

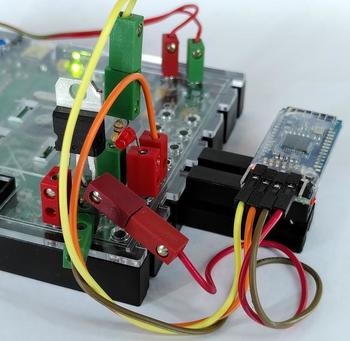
www/manual/experimente/hm10_bidir_7805_2.jpg
