harbaum/ftduino/www/manual/experimente/hm10_kabel.jpg

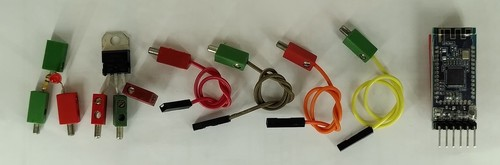
www/manual/experimente/hm10_kabel.jpg
