harbaum/ftduino/www/manual/experimente/hm10_serial1_bidir_7805_svg.png

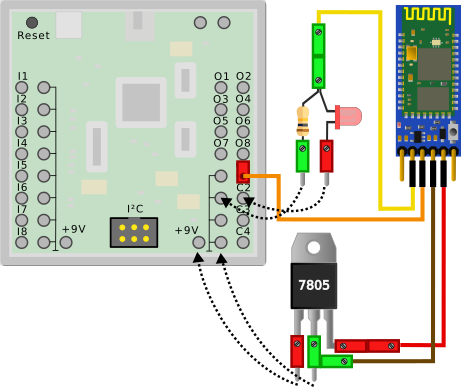
www/manual/experimente/hm10_serial1_bidir_7805_svg.png
