harbaum/ftduino/www/manual/experimente/hm10_serial1_svg.png

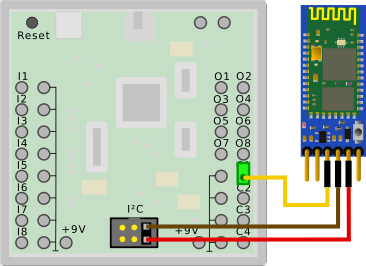
www/manual/experimente/hm10_serial1_svg.png
