harbaum/ftduino/www/manual/experimente/i2c_digispark.jpg

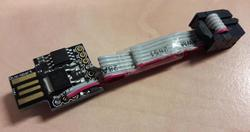
www/manual/experimente/i2c_digispark.jpg
