harbaum/ftduino/www/manual/experimente/i2c_ext_sens_svg.png

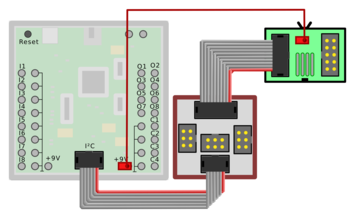
www/manual/experimente/i2c_ext_sens_svg.png
