harbaum/ftduino/www/manual/experimente/i2c_master_client_svg.png

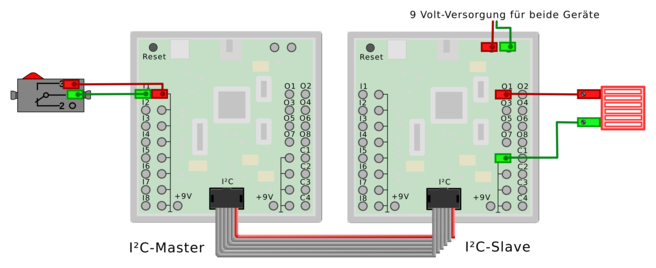
www/manual/experimente/i2c_master_client_svg.png
