harbaum/ftduino/www/manual/experimente/i2c_uart_hm10.jpg

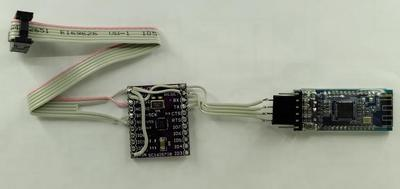
www/manual/experimente/i2c_uart_hm10.jpg
