harbaum/ftduino/www/manual/experimente/i2c_uart_svg.png

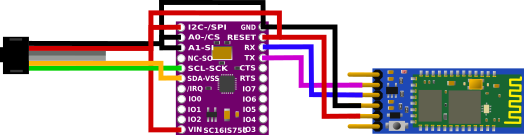
www/manual/experimente/i2c_uart_svg.png
