harbaum/ftduino/www/manual/experimente/i2c_x4.jpg

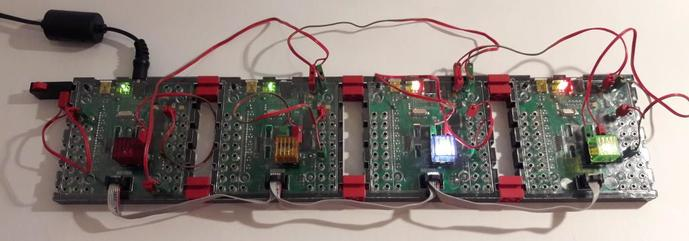
www/manual/experimente/i2c_x4.jpg
