harbaum/ftduino/www/manual/experimente/i2c_x4_svg.png

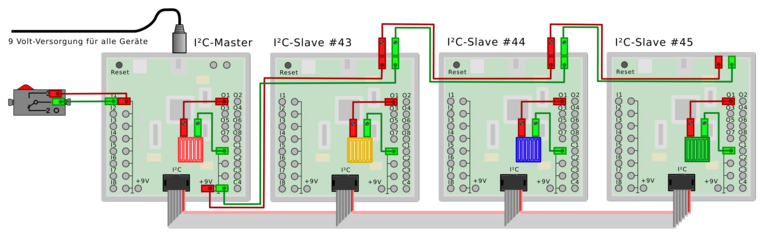
www/manual/experimente/i2c_x4_svg.png
