harbaum/ftduino/www/manual/experimente/i2cscanner_mpu6050.png

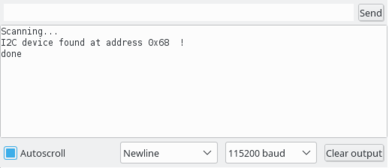
www/manual/experimente/i2cscanner_mpu6050.png
