harbaum/ftduino/www/manual/experimente/input_led_svg.png

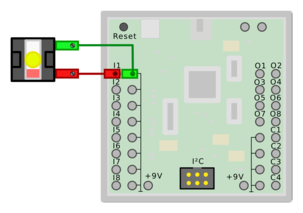
www/manual/experimente/input_led_svg.png
