harbaum/ftduino/www/manual/experimente/lamptimer_svg.png

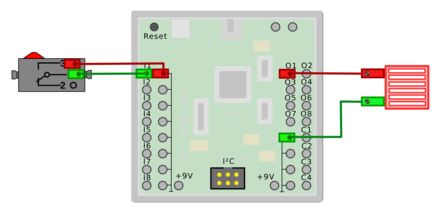
www/manual/experimente/lamptimer_svg.png
