harbaum/ftduino/www/manual/experimente/mini_i2c_adapter.jpg

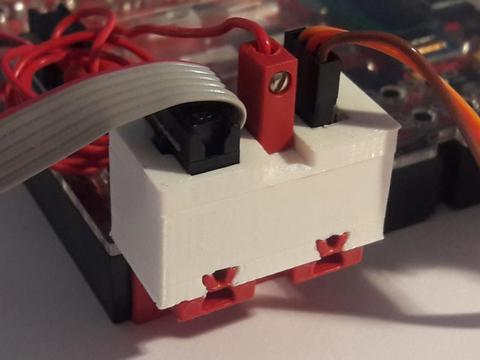
www/manual/experimente/mini_i2c_adapter.jpg
