harbaum/ftduino/www/manual/experimente/mini_servo_adapter_45_svg.png

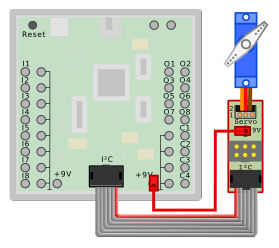
www/manual/experimente/mini_servo_adapter_45_svg.png
