harbaum/ftduino/www/manual/experimente/mini_servo_address.png

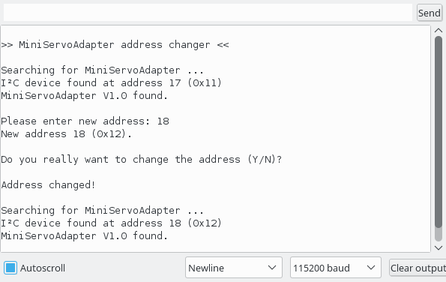
www/manual/experimente/mini_servo_address.png
