harbaum/ftduino/www/manual/experimente/motorbrake_svg.png

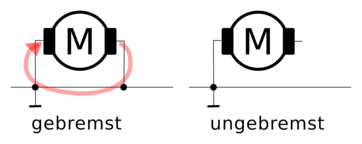
www/manual/experimente/motorbrake_svg.png
