harbaum/ftduino/www/manual/experimente/mpu6050_serieller_monitor.png

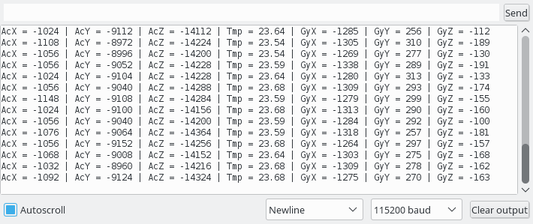
www/manual/experimente/mpu6050_serieller_monitor.png
