harbaum/ftduino/www/manual/experimente/music_svg.png

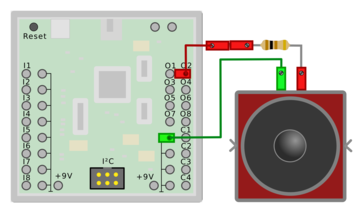
www/manual/experimente/music_svg.png
