harbaum/ftduino/www/manual/experimente/pwm_move_svg.png

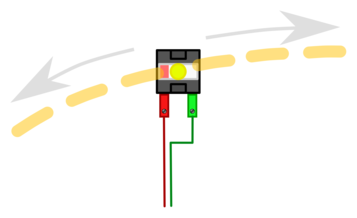
www/manual/experimente/pwm_move_svg.png
