harbaum/ftduino/www/manual/experimente/pwm_percent_svg.png

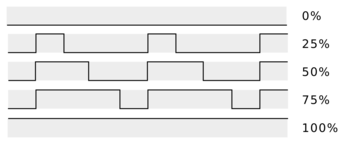
www/manual/experimente/pwm_percent_svg.png
