harbaum/ftduino/www/manual/experimente/pwmspeed_svg.png

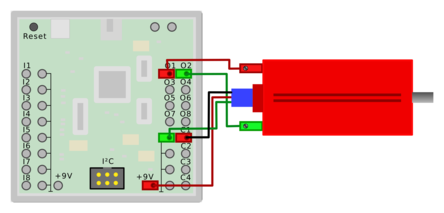
www/manual/experimente/pwmspeed_svg.png
