harbaum/ftduino/www/manual/experimente/schema_mpu6050_svg.png

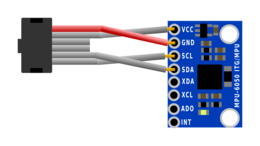
www/manual/experimente/schema_mpu6050_svg.png
