harbaum/ftduino/www/manual/experimente/schrittmotor.jpg

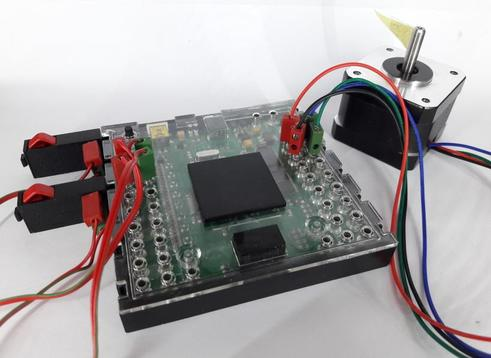
www/manual/experimente/schrittmotor.jpg
