harbaum/ftduino/www/manual/experimente/schrittmotor_schema_svg.png

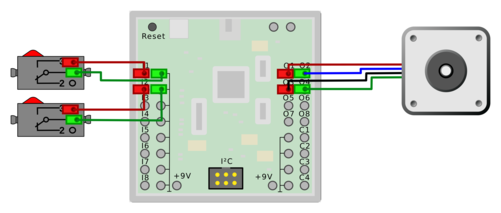
www/manual/experimente/schrittmotor_schema_svg.png
