harbaum/ftduino/www/manual/experimente/schrittmotor_svg.png

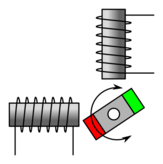
www/manual/experimente/schrittmotor_svg.png
