harbaum/ftduino/www/manual/experimente/schrittmotor_vollschritt_svg.png

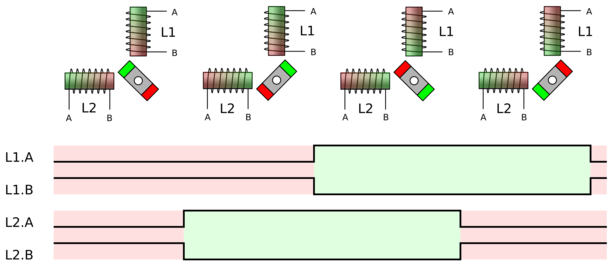
www/manual/experimente/schrittmotor_vollschritt_svg.png
