harbaum/ftduino/www/manual/experimente/screenshot_arduinoblue_1.png

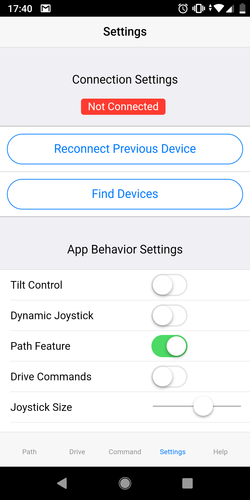
www/manual/experimente/screenshot_arduinoblue_1.png
