harbaum/ftduino/www/manual/experimente/screenshot_arduinoblue_2.png

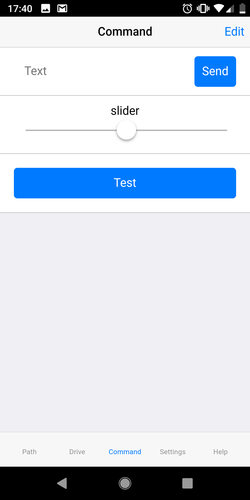
www/manual/experimente/screenshot_arduinoblue_2.png
