harbaum/ftduino/www/manual/experimente/screenshot_arduinoblue_3.png

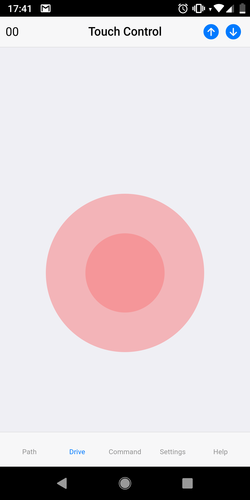
www/manual/experimente/screenshot_arduinoblue_3.png
