harbaum/ftduino/www/manual/experimente/screenshot_win_bluetooth_1.png

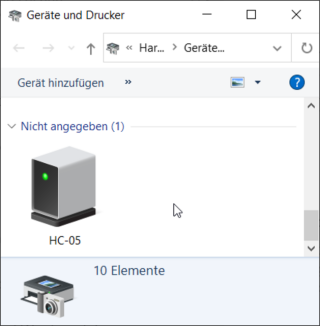
www/manual/experimente/screenshot_win_bluetooth_1.png
