harbaum/ftduino/www/manual/experimente/screenshot_win_bluetooth_2.png

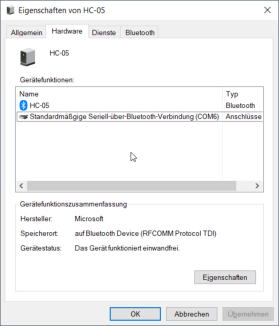
www/manual/experimente/screenshot_win_bluetooth_2.png
