harbaum/ftduino/www/manual/experimente/screenshot_win_bluetooth_3.png

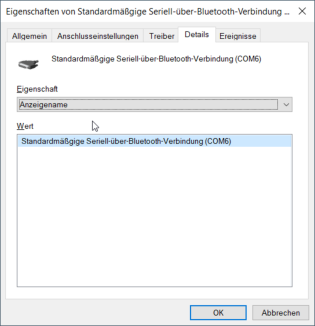
www/manual/experimente/screenshot_win_bluetooth_3.png
