harbaum/ftduino/www/manual/experimente/servo.jpg

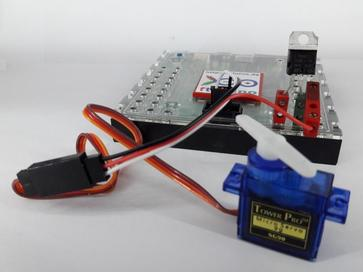
www/manual/experimente/servo.jpg
