harbaum/ftduino/www/manual/experimente/servo_7806_svg.png

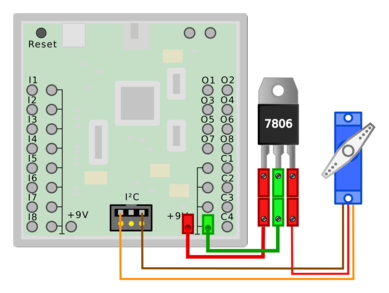
www/manual/experimente/servo_7806_svg.png
