harbaum/ftduino/www/manual/experimente/servo_cable.jpg

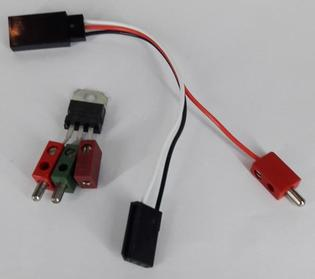
www/manual/experimente/servo_cable.jpg
