harbaum/ftduino/www/manual/experimente/servo_signal_svg.png

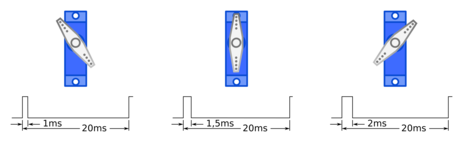
www/manual/experimente/servo_signal_svg.png
