harbaum/ftduino/www/manual/experimente/servo_svg.png

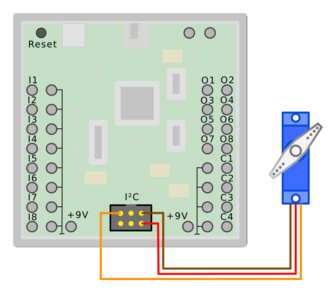
www/manual/experimente/servo_svg.png
