harbaum/ftduino/www/manual/experimente/temperature_svg.png

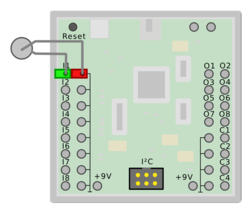
www/manual/experimente/temperature_svg.png
