harbaum/ftduino/www/manual/experimente/tristate_svg.png

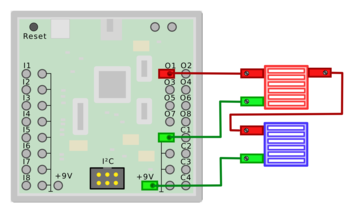
www/manual/experimente/tristate_svg.png
