harbaum/ftduino/www/manual/experimente/vl53l0x_schema_svg.png

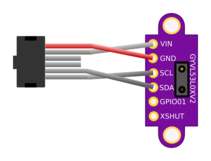
www/manual/experimente/vl53l0x_schema_svg.png
