harbaum/ftduino/www/manual/experimente/webusb_android.png

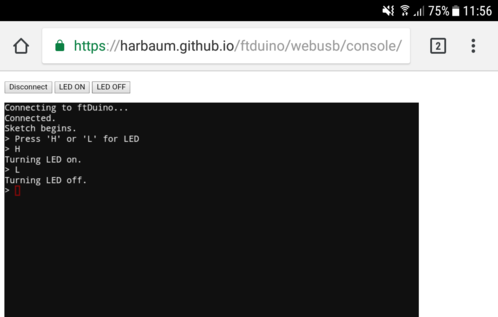
www/manual/experimente/webusb_android.png
