harbaum/ftduino/www/manual/experimente/webusb_console.png

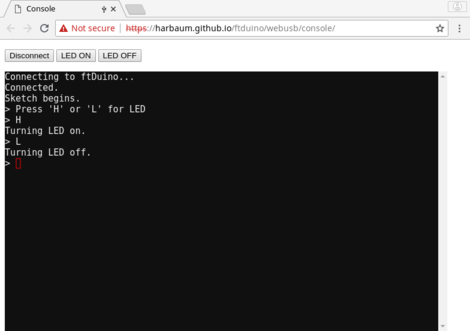
www/manual/experimente/webusb_console.png
