harbaum/ftduino/www/manual/experimente/webusb_hinweis.png

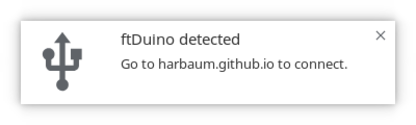
www/manual/experimente/webusb_hinweis.png
