harbaum/ftduino/www/manual/experimente/ws2812b_svg.png

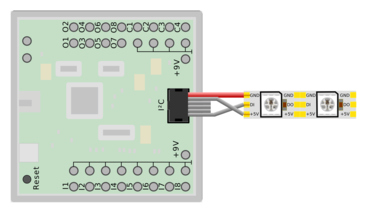
www/manual/experimente/ws2812b_svg.png
